jotego/jtcps/doc/measurements/dma/pcb.jpg

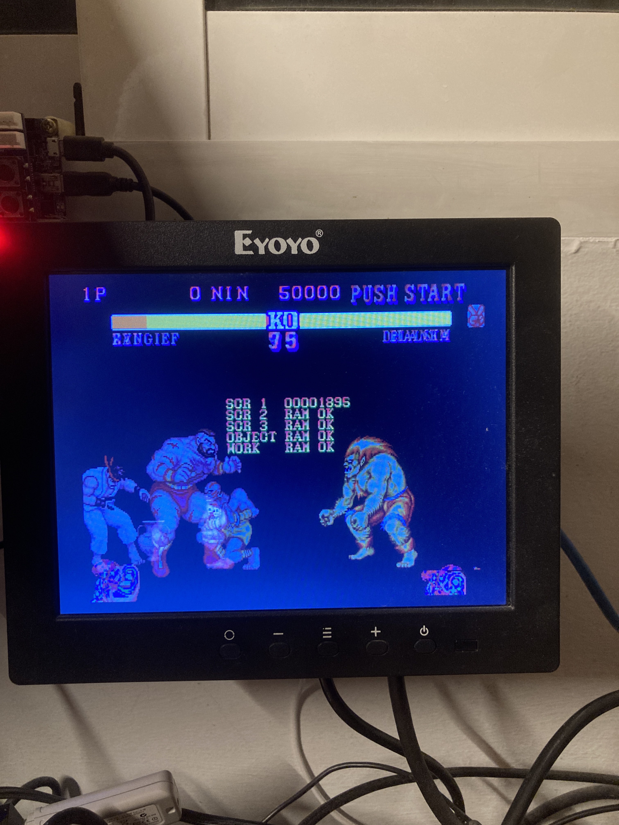
doc/measurements/dma/pcb.jpg
