jotego/jtcps/cores/cps15/ver/game/dino/1.png

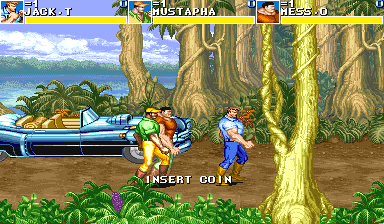
cores/cps15/ver/game/dino/1.png
