jotego/jtcps/cores/cps1/ver/game/sf2/5.png

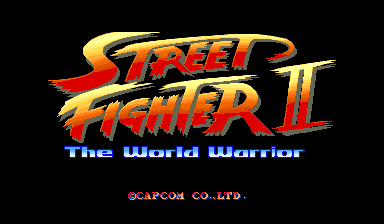
cores/cps1/ver/game/sf2/5.png
