jotego/jtcps/cores/cps1/ver/gfx/0000.png

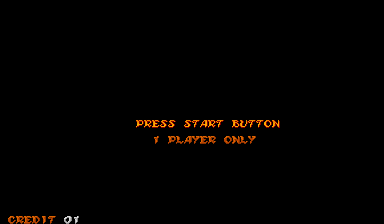
cores/cps1/ver/gfx/0000.png
