jotego/jtcps/cores/cps1/ver/gfx/0001.png

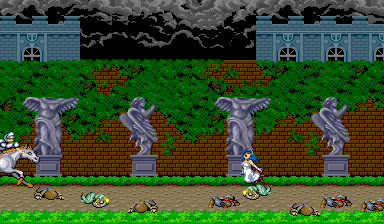
cores/cps1/ver/gfx/0001.png
