jotego/jtcps/doc/cps1-sound/fm_response.png

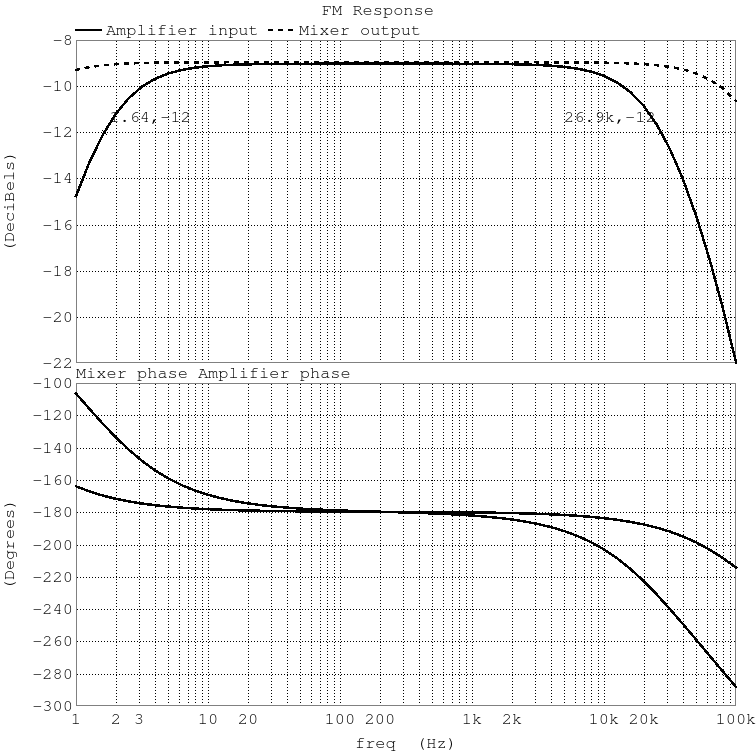
doc/cps1-sound/fm_response.png
