jotego/jtcps/doc/cps1-sound/pcm_response.png

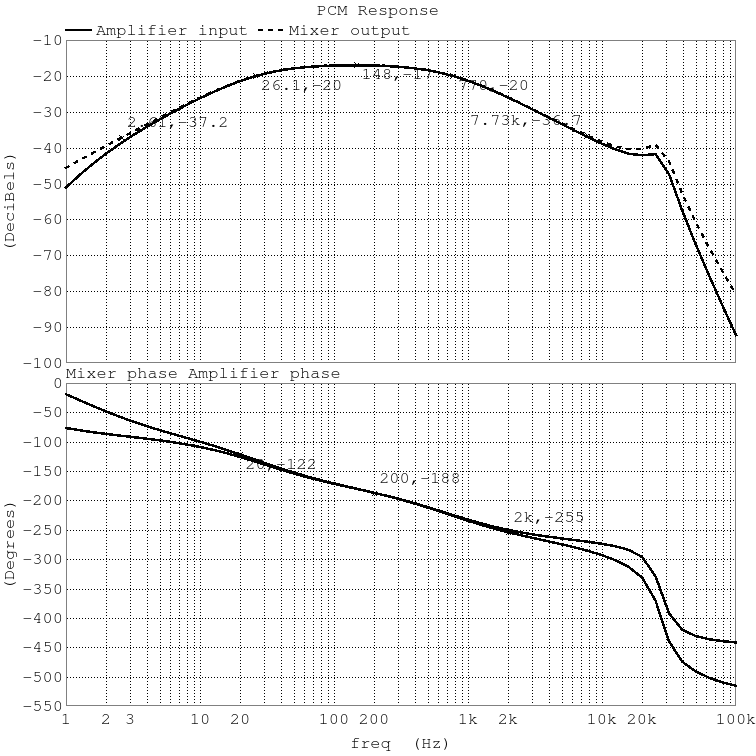
doc/cps1-sound/pcm_response.png
