jotego/jtcps/doc/cps1-sound/fm_step.png

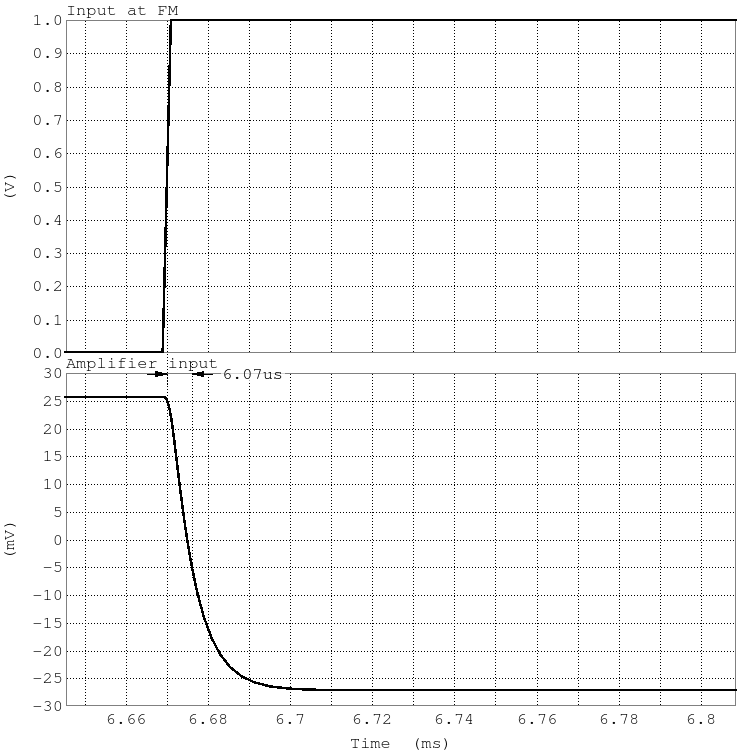
doc/cps1-sound/fm_step.png
