jotego/jtcps/doc/cps1-sound/pcm_step.png

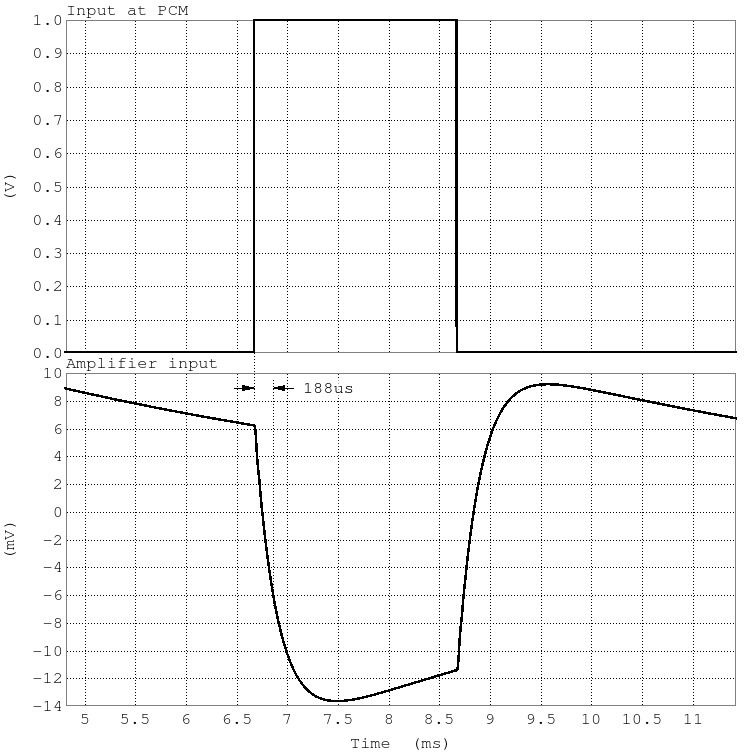
doc/cps1-sound/pcm_step.png
