jotego/jtcps/doc/measurements/DS1Z_QuickPrint2.png

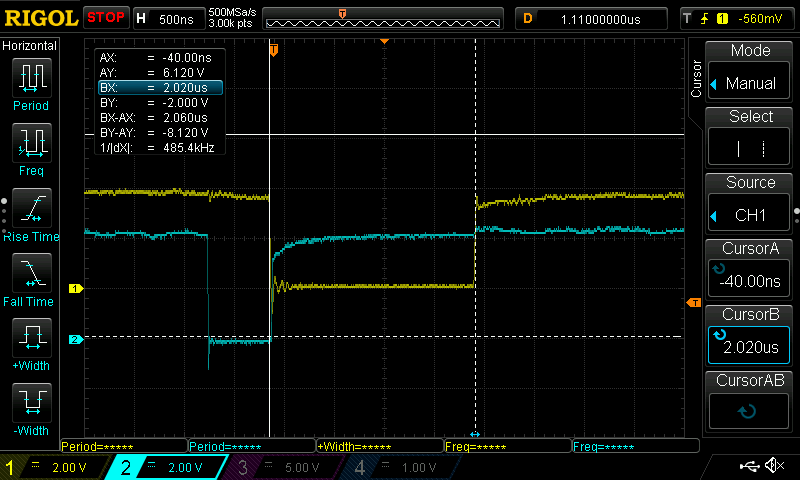
doc/measurements/DS1Z_QuickPrint2.png
