jotego/jtcps/doc/measurements/DS1Z_QuickPrint3.png

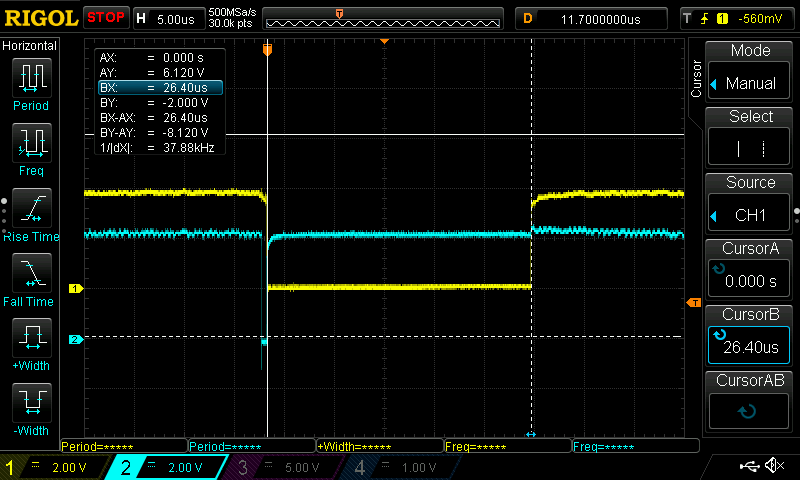
doc/measurements/DS1Z_QuickPrint3.png
