jotego/jtcps/doc/measurements/DS1Z_QuickPrint4.png

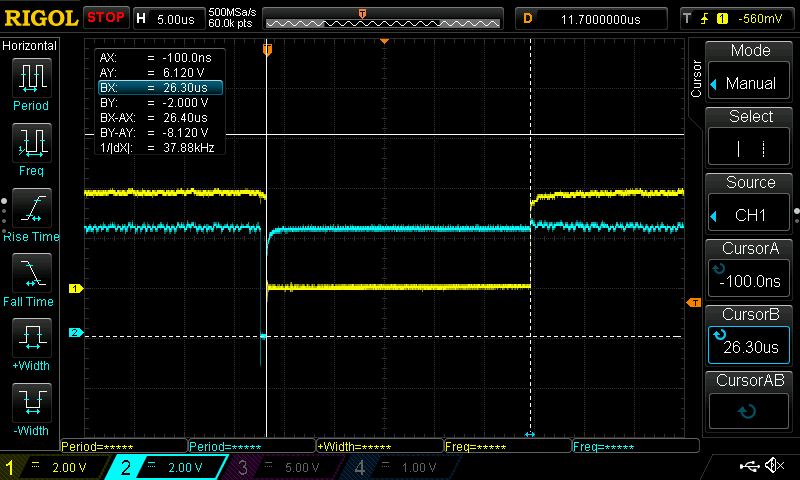
doc/measurements/DS1Z_QuickPrint4.png
