jotego/jtcps/doc/measurements/DS1Z_QuickPrint7.png

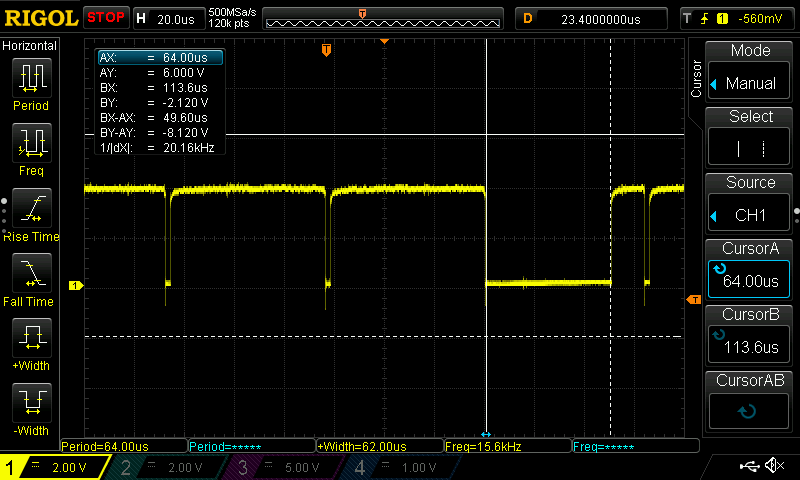
doc/measurements/DS1Z_QuickPrint7.png
