jotego/jtcps/doc/measurements/DS1Z_QuickPrint8.png

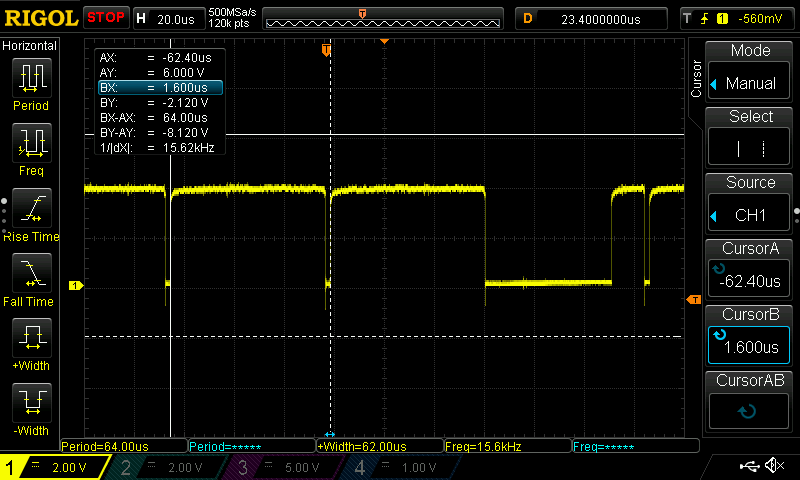
doc/measurements/DS1Z_QuickPrint8.png
