jotego/jtcps/doc/measurements/DS1Z_QuickPrint10.png

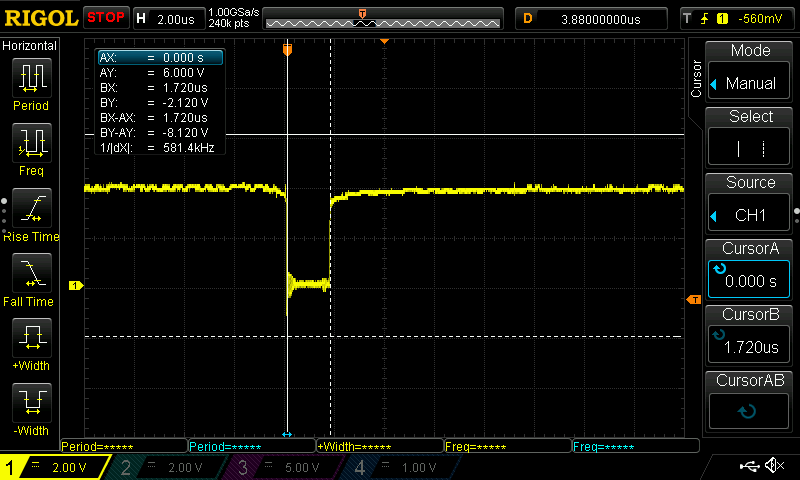
doc/measurements/DS1Z_QuickPrint10.png
