jotego/jtcps/doc/measurements/DS1Z_QuickPrint11.png

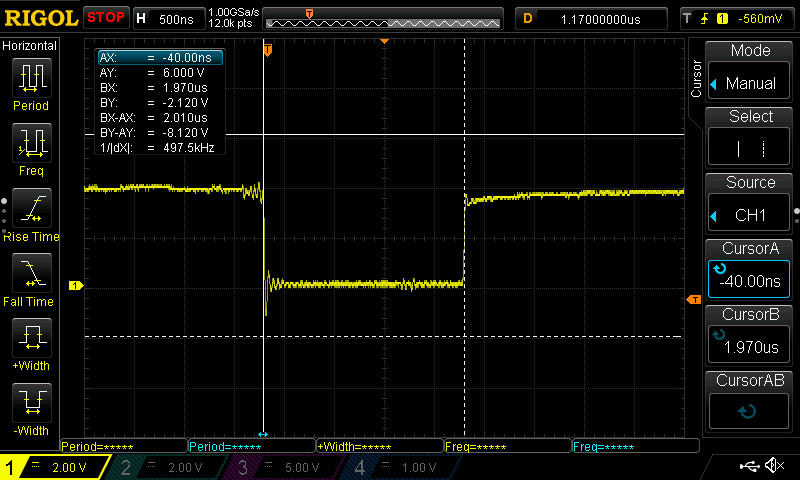
doc/measurements/DS1Z_QuickPrint11.png
