jotego/jtcps/doc/measurements/DS1Z_QuickPrint13.png

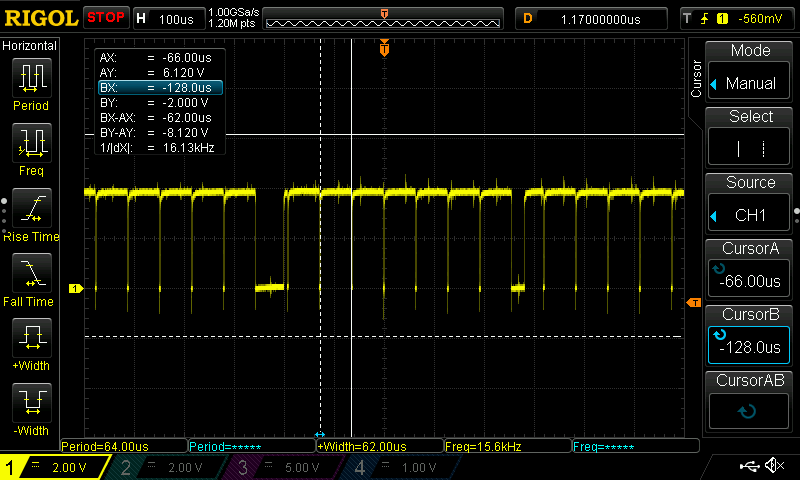
doc/measurements/DS1Z_QuickPrint13.png
