jotego/jtcps/doc/measurements/DS1Z_QuickPrint14.png

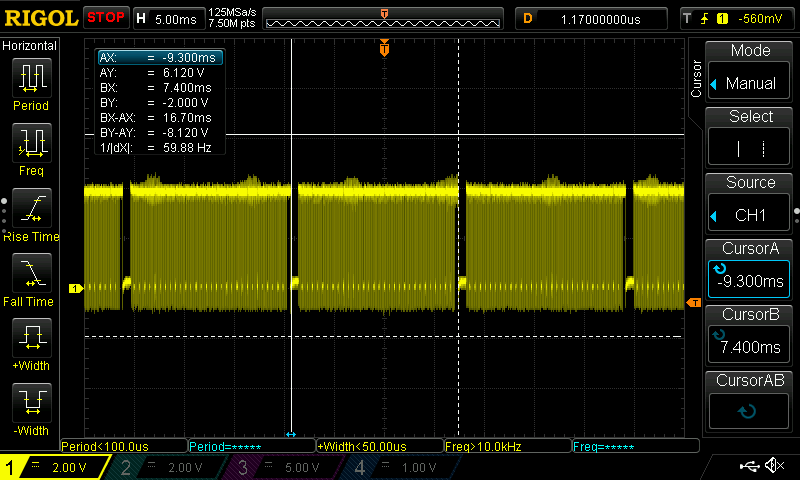
doc/measurements/DS1Z_QuickPrint14.png
