jotego/jtcps/doc/measurements/DS1Z_QuickPrint15.png

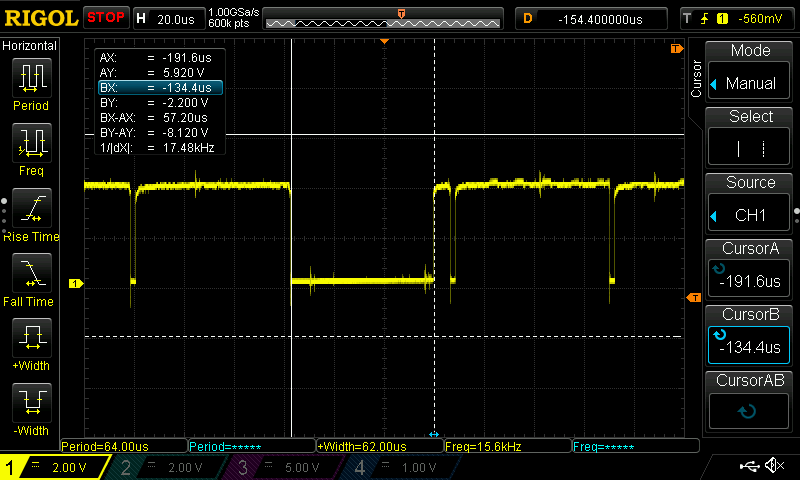
doc/measurements/DS1Z_QuickPrint15.png
