jotego/jtcps/doc/measurements/DS1Z_QuickPrint17.png

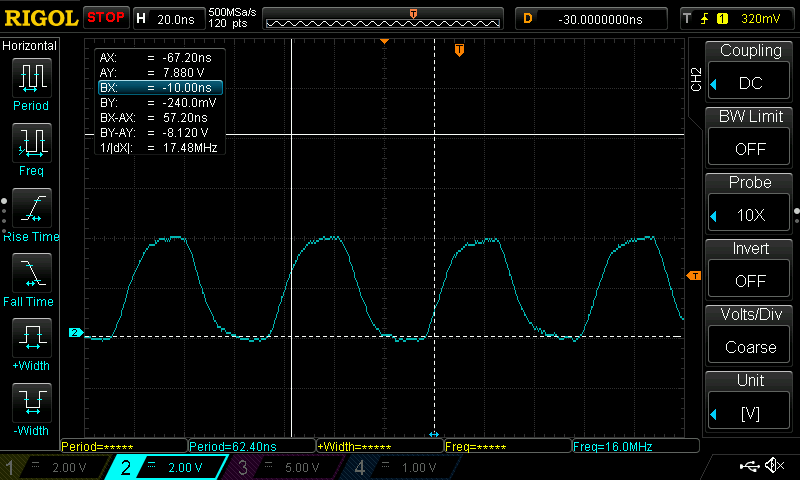
doc/measurements/DS1Z_QuickPrint17.png
