jotego/jtcps/doc/measurements/dma/20210130_182909-screen.png

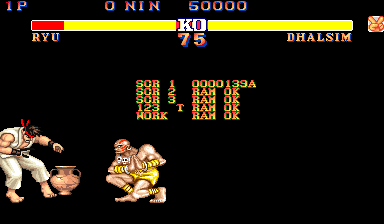
doc/measurements/dma/20210130_182909-screen.png
