jotego/jtcps/doc/measurements/dma/20210130_182920-screen.png

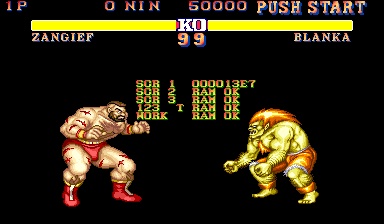
doc/measurements/dma/20210130_182920-screen.png
