jotego/jtcps/doc/measurements/dma/20210130_182930-screen.png

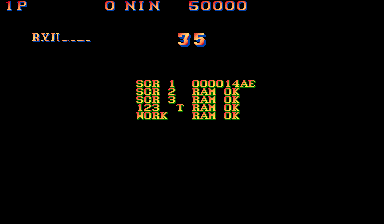
doc/measurements/dma/20210130_182930-screen.png
