jotego/jtcps/cores/cps3/memories.kicad_sch

## KiCad design cores/cps3/memories.kicad_sch (2022-10-21)

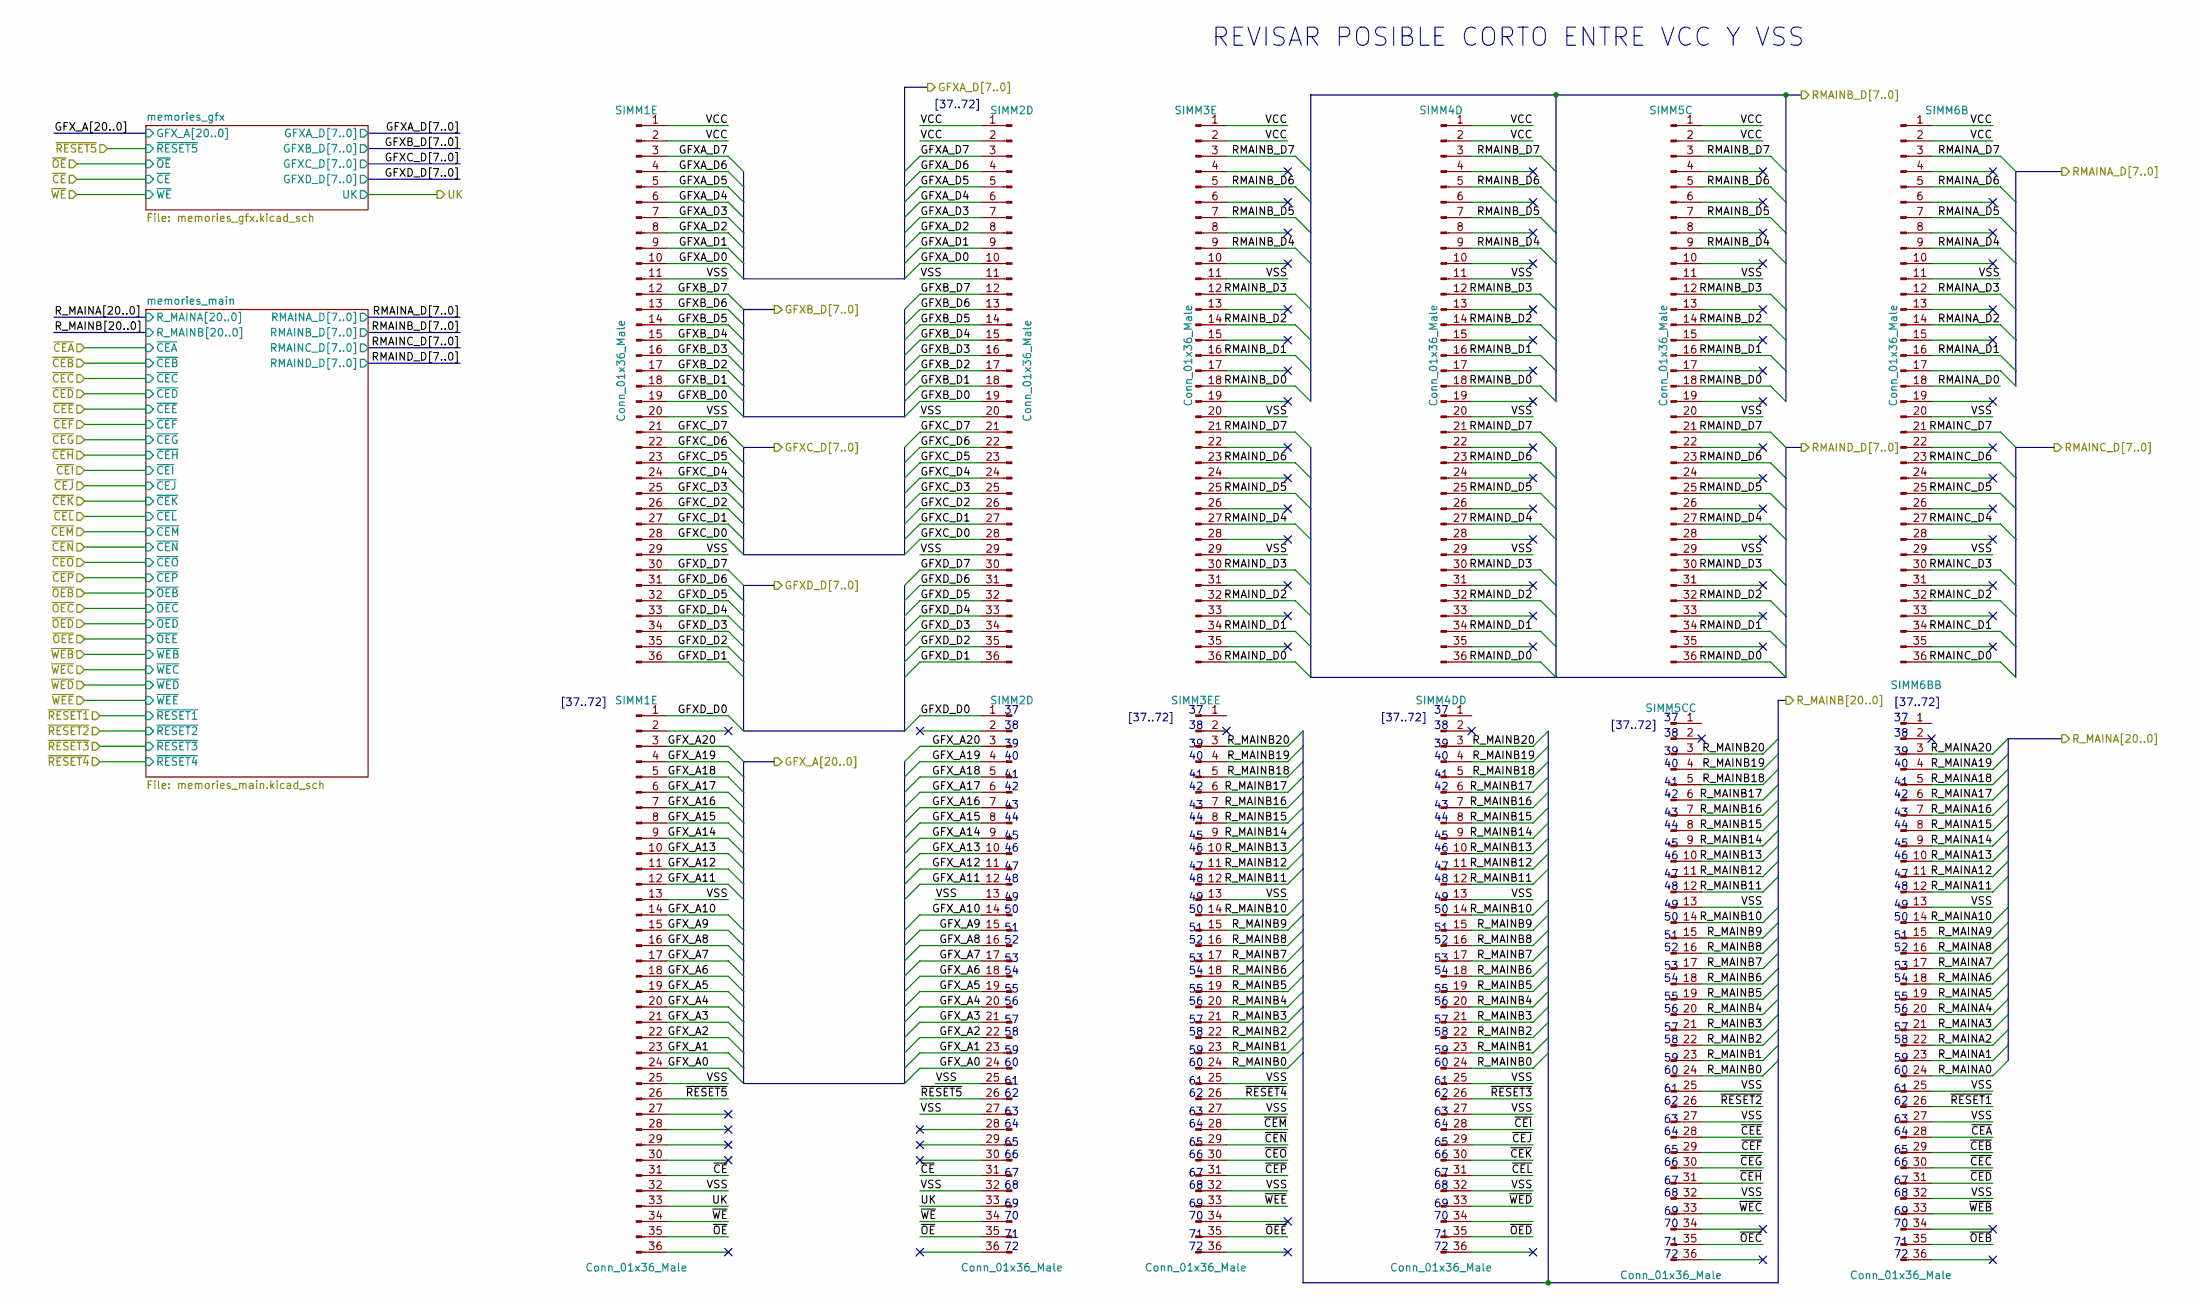
[picture p86: schematic memories.kicad_sch]

Parts:
SIMM1E, SIMM2D, SIMM3E, SIMM3EE, SIMM4D, SIMM4DD, SIMM5C, SIMM5CC, SIMM6B, SIMM6BB: Conn_01x36_Male

Connections:
GFXA_D0: SIMM1E.10, SIMM2D.10
GFXA_D1: SIMM1E.9, SIMM2D.9
GFXA_D2: SIMM1E.8, SIMM2D.8
GFXA_D3: SIMM1E.7, SIMM2D.7
GFXA_D4: SIMM1E.6, SIMM2D.6
GFXA_D5: SIMM1E.5, SIMM2D.5
GFXA_D6: SIMM1E.4, SIMM2D.4
GFXA_D7: SIMM1E.3, SIMM2D.3
GFXB_D0: SIMM1E.19, SIMM2D.19
GFXB_D1: SIMM1E.18, SIMM2D.18
GFXB_D2: SIMM1E.17, SIMM2D.17
GFXB_D3: SIMM1E.16, SIMM2D.16
GFXB_D4: SIMM1E.15, SIMM2D.15
GFXB_D5: SIMM1E.14, SIMM2D.14
GFXB_D6: SIMM1E.13, SIMM2D.13
GFXB_D7: SIMM1E.12, SIMM2D.12
GFXC_D0: SIMM1E.28, SIMM2D.28
GFXC_D1: SIMM1E.27, SIMM2D.27
GFXC_D2: SIMM1E.26, SIMM2D.26
GFXC_D3: SIMM1E.25, SIMM2D.25
GFXC_D4: SIMM1E.24, SIMM2D.24
GFXC_D5: SIMM1E.23, SIMM2D.23
GFXC_D6: SIMM1E.22, SIMM2D.22
GFXC_D7: SIMM1E.21, SIMM2D.21
GFXD_D0: SIMM1E.1, SIMM2D.1
GFXD_D1: SIMM1E.36, SIMM2D.36
GFXD_D2: SIMM1E.35, SIMM2D.35
GFXD_D3: SIMM1E.34, SIMM2D.34
GFXD_D4: SIMM1E.33, SIMM2D.33
GFXD_D5: SIMM1E.32, SIMM2D.32
GFXD_D6: SIMM1E.31, SIMM2D.31
GFXD_D7: SIMM1E.30, SIMM2D.30
GFX_A0: SIMM1E.24, SIMM2D.24
GFX_A1: SIMM1E.23, SIMM2D.23
GFX_A2: SIMM1E.22, SIMM2D.22
GFX_A3: SIMM1E.21, SIMM2D.21
GFX_A4: SIMM1E.20, SIMM2D.20
GFX_A5: SIMM1E.19, SIMM2D.19
GFX_A6: SIMM1E.18, SIMM2D.18
GFX_A7: SIMM1E.17, SIMM2D.17
GFX_A8: SIMM1E.16, SIMM2D.16
GFX_A9: SIMM1E.15, SIMM2D.15
GFX_A10: SIMM1E.14, SIMM2D.14
GFX_A11: SIMM1E.12, SIMM2D.12
GFX_A12: SIMM1E.11, SIMM2D.11
GFX_A13: SIMM1E.10, SIMM2D.10
GFX_A14: SIMM1E.9, SIMM2D.9
GFX_A15: SIMM1E.8, SIMM2D.8
GFX_A16: SIMM1E.7, SIMM2D.7
GFX_A17: SIMM1E.6, SIMM2D.6
GFX_A18: SIMM1E.5, SIMM2D.5
GFX_A19: SIMM1E.4, SIMM2D.4
GFX_A20: SIMM1E.3, SIMM2D.3
RMAINA_D0: SIMM6B.18
RMAINA_D1: SIMM6B.16
RMAINA_D2: SIMM6B.14
RMAINA_D3: SIMM6B.12
RMAINA_D4: SIMM6B.9
RMAINA_D5: SIMM6B.7
RMAINA_D6: SIMM6B.5
RMAINA_D7: SIMM6B.3
RMAINB_D0: SIMM3E.18, SIMM4D.18, SIMM5C.18
RMAINB_D1: SIMM3E.16, SIMM4D.16, SIMM5C.16
RMAINB_D2: SIMM3E.14, SIMM4D.14, SIMM5C.14
RMAINB_D3: SIMM3E.12, SIMM4D.12, SIMM5C.12
RMAINB_D4: SIMM3E.9, SIMM4D.9, SIMM5C.9
RMAINB_D5: SIMM3E.7, SIMM4D.7, SIMM5C.7
RMAINB_D6: SIMM3E.5, SIMM4D.5, SIMM5C.5
RMAINB_D7: SIMM3E.3, SIMM4D.3, SIMM5C.3
RMAINC_D0: SIMM6B.36
RMAINC_D1: SIMM6B.34
RMAINC_D2: SIMM6B.32
RMAINC_D3: SIMM6B.30
RMAINC_D4: SIMM6B.27
RMAINC_D5: SIMM6B.25
RMAINC_D6: SIMM6B.23
RMAINC_D7: SIMM6B.21
RMAIND_D0: SIMM3E.36, SIMM4D.36, SIMM5C.36
RMAIND_D1: SIMM3E.34, SIMM4D.34, SIMM5C.34
RMAIND_D2: SIMM3E.32, SIMM4D.32, SIMM5C.32
RMAIND_D3: SIMM3E.30, SIMM4D.30, SIMM5C.30
RMAIND_D4: SIMM3E.27, SIMM4D.27, SIMM5C.27
RMAIND_D5: SIMM3E.25, SIMM4D.25, SIMM5C.25
RMAIND_D6: SIMM3E.23, SIMM4D.23, SIMM5C.23
RMAIND_D7: SIMM3E.21, SIMM4D.21, SIMM5C.21
R_MAINA0: SIMM6BB.24
R_MAINA1: SIMM6BB.23
R_MAINA2: SIMM6BB.22
R_MAINA3: SIMM6BB.21
R_MAINA4: SIMM6BB.20
R_MAINA5: SIMM6BB.19
R_MAINA6: SIMM6BB.18
R_MAINA7: SIMM6BB.17
R_MAINA8: SIMM6BB.16
R_MAINA9: SIMM6BB.15
R_MAINA10: SIMM6BB.14
R_MAINA11: SIMM6BB.12
R_MAINA12: SIMM6BB.11
R_MAINA13: SIMM6BB.10
R_MAINA14: SIMM6BB.9
R_MAINA15: SIMM6BB.8
R_MAINA16: SIMM6BB.7
R_MAINA17: SIMM6BB.6
R_MAINA18: SIMM6BB.5
R_MAINA19: SIMM6BB.4
R_MAINA20: SIMM6BB.3
R_MAINB0: SIMM3EE.24, SIMM4DD.24, SIMM5CC.24
R_MAINB1: SIMM3EE.23, SIMM4DD.23, SIMM5CC.23
R_MAINB2: SIMM3EE.22, SIMM4DD.22, SIMM5CC.22
R_MAINB3: SIMM3EE.21, SIMM4DD.21, SIMM5CC.21
R_MAINB4: SIMM3EE.20, SIMM4DD.20, SIMM5CC.20
R_MAINB5: SIMM3EE.19, SIMM4DD.19, SIMM5CC.19
R_MAINB6: SIMM3EE.18, SIMM4DD.18, SIMM5CC.18
R_MAINB7: SIMM3EE.17, SIMM4DD.17, SIMM5CC.17
R_MAINB8: SIMM3EE.16, SIMM4DD.16, SIMM5CC.16
R_MAINB9: SIMM3EE.15, SIMM4DD.15, SIMM5CC.15
R_MAINB10: SIMM3EE.14, SIMM4DD.14, SIMM5CC.14
R_MAINB11: SIMM3EE.12, SIMM4DD.12, SIMM5CC.12
R_MAINB12: SIMM3EE.11, SIMM4DD.11, SIMM5CC.11
R_MAINB13: SIMM3EE.10, SIMM4DD.10, SIMM5CC.10
R_MAINB14: SIMM3EE.9, SIMM4DD.9, SIMM5CC.9
R_MAINB15: SIMM3EE.8, SIMM4DD.8, SIMM5CC.8
R_MAINB16: SIMM3EE.7, SIMM4DD.7, SIMM5CC.7
R_MAINB17: SIMM3EE.6, SIMM4DD.6, SIMM5CC.6
R_MAINB18: SIMM3EE.5, SIMM4DD.5, SIMM5CC.5
R_MAINB19: SIMM3EE.4, SIMM4DD.4, SIMM5CC.4
R_MAINB20: SIMM3EE.3, SIMM4DD.3, SIMM5CC.3
UK: SIMM1E.33, SIMM2D.33
VCC: SIMM1E.1, SIMM1E.2, SIMM2D.1, SIMM2D.2, SIMM3E.1, SIMM3E.2, SIMM4D.1, SIMM4D.2, SIMM5C.1, SIMM5C.2, SIMM6B.1, SIMM6B.2
VSS: SIMM1E.11, SIMM1E.13, SIMM1E.20, SIMM1E.25, SIMM1E.29, SIMM1E.32, SIMM2D.11, SIMM2D.13, SIMM2D.20, SIMM2D.25, SIMM2D.27, SIMM2D.29, SIMM2D.32, SIMM3E.11, SIMM3E.20, SIMM3E.29, SIMM3EE.13, SIMM3EE.25, SIMM3EE.27, SIMM3EE.32, SIMM4D.11, SIMM4D.20, SIMM4D.29, SIMM4DD.13, SIMM4DD.25, SIMM4DD.27, SIMM4DD.32, SIMM5C.11, SIMM5C.20, SIMM5C.29, SIMM5CC.13, SIMM5CC.25, SIMM5CC.27, SIMM5CC.32, SIMM6B.11, SIMM6B.20, SIMM6B.29, SIMM6BB.13, SIMM6BB.25, SIMM6BB.27, SIMM6BB.32
~CEA: SIMM6BB.28
~CEB: SIMM6BB.29
~CEC: SIMM6BB.30
~CED: SIMM6BB.31
~CEE: SIMM5CC.28
~CEF: SIMM5CC.29
~CEG: SIMM5CC.30
~CEH: SIMM5CC.31
~CEI: SIMM4DD.28
~CEJ: SIMM4DD.29
~CEK: SIMM4DD.30
~CEL: SIMM4DD.31
~CEM: SIMM3EE.28
~CEN: SIMM3EE.29
~CEO: SIMM3EE.30
~CEP: SIMM3EE.31
~CE: SIMM1E.31, SIMM2D.31
~OEB: SIMM6BB.35
~OEC: SIMM5CC.35
~OED: SIMM4DD.35
~OEE: SIMM3EE.35
~OE: SIMM1E.35, SIMM2D.35
~RESET1: SIMM6BB.26
~RESET2: SIMM5CC.26
~RESET3: SIMM4DD.26
~RESET4: SIMM3EE.26
~RESET5: SIMM1E.26, SIMM2D.26
~WEB: SIMM6BB.33
~WEC: SIMM5CC.33
~WED: SIMM4DD.33
~WEE: SIMM3EE.33
~WE: SIMM1E.34, SIMM2D.34

Notes on the sheet:
59 60
63 64
57 58
39 40
67 68
65 66
55 56
71 72
69 70
61 62
45 46
41 42
53 54
43 44
49 50
47 48
[37..72]
REVISAR POSIBLE CORTO ENTRE VCC Y VSS
51 52
