jotego/jtcps/cores/cps3/memories_gfx.kicad_sch

## KiCad design cores/cps3/memories_gfx.kicad_sch (2022-10-21)

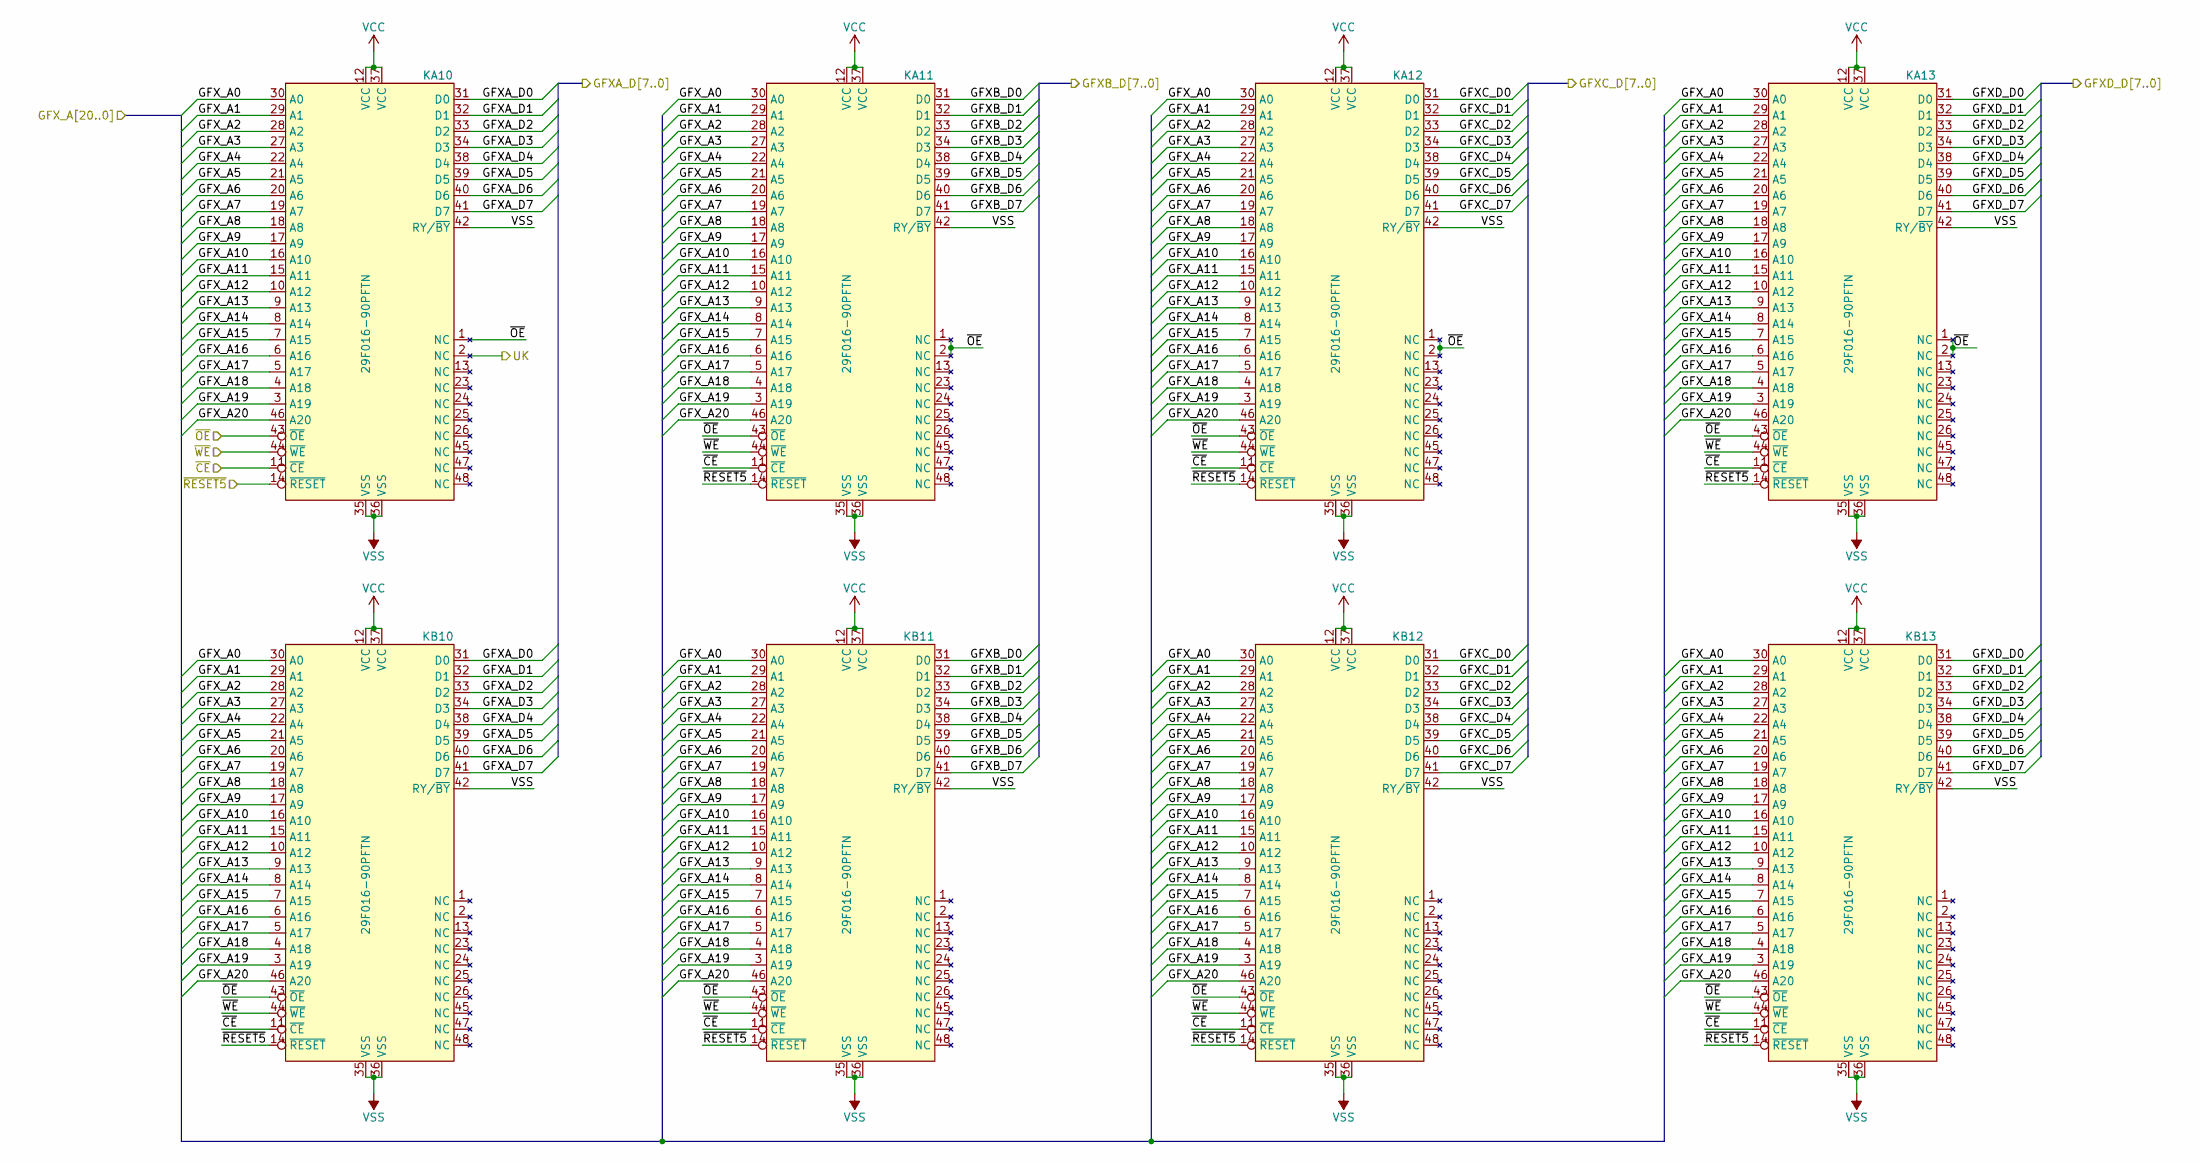
[picture p87: schematic memories_gfx.kicad_sch]

Parts:
KA10, KA11, KA12, KA13: 29F016-90PFTN
KB10, KB11, KB12, KB13: 29F016-90PFTN

Connections:
GFXA_D0: KA10.31 (D0), KB10.31 (D0)
GFXA_D1: KA10.32 (D1), KB10.32 (D1)
GFXA_D2: KA10.33 (D2), KB10.33 (D2)
GFXA_D3: KA10.34 (D3), KB10.34 (D3)
GFXA_D4: KA10.38 (D4), KB10.38 (D4)
GFXA_D5: KA10.39 (D5), KB10.39 (D5)
GFXA_D6: KA10.40 (D6), KB10.40 (D6)
GFXA_D7: KA10.41 (D7), KB10.41 (D7)
GFXB_D0: KA11.31 (D0), KB11.31 (D0)
GFXB_D1: KA11.32 (D1), KB11.32 (D1)
GFXB_D2: KA11.33 (D2), KB11.33 (D2)
GFXB_D3: KA11.34 (D3), KB11.34 (D3)
GFXB_D4: KA11.38 (D4), KB11.38 (D4)
GFXB_D5: KA11.39 (D5), KB11.39 (D5)
GFXB_D6: KA11.40 (D6), KB11.40 (D6)
GFXB_D7: KA11.41 (D7), KB11.41 (D7)
GFXC_D0: KA12.31 (D0), KB12.31 (D0)
GFXC_D1: KA12.32 (D1), KB12.32 (D1)
GFXC_D2: KA12.33 (D2), KB12.33 (D2)
GFXC_D3: KA12.34 (D3), KB12.34 (D3)
GFXC_D4: KA12.38 (D4), KB12.38 (D4)
GFXC_D5: KA12.39 (D5), KB12.39 (D5)
GFXC_D6: KA12.40 (D6), KB12.40 (D6)
GFXC_D7: KA12.41 (D7), KB12.41 (D7)
GFXD_D0: KA13.31 (D0), KB13.31 (D0)
GFXD_D1: KA13.32 (D1), KB13.32 (D1)
GFXD_D2: KA13.33 (D2), KB13.33 (D2)
GFXD_D3: KA13.34 (D3), KB13.34 (D3)
GFXD_D4: KA13.38 (D4), KB13.38 (D4)
GFXD_D5: KA13.39 (D5), KB13.39 (D5)
GFXD_D6: KA13.40 (D6), KB13.40 (D6)
GFXD_D7: KA13.41 (D7), KB13.41 (D7)
GFX_A0: KA10.30 (A0), KA11.30 (A0), KA12.30 (A0), KA13.30 (A0), KB10.30 (A0), KB11.30 (A0), KB12.30 (A0), KB13.30 (A0)
GFX_A1: KA10.29 (A1), KA11.29 (A1), KA12.29 (A1), KA13.29 (A1), KB10.29 (A1), KB11.29 (A1), KB12.29 (A1), KB13.29 (A1)
GFX_A2: KA10.28 (A2), KA11.28 (A2), KA12.28 (A2), KA13.28 (A2), KB10.28 (A2), KB11.28 (A2), KB12.28 (A2), KB13.28 (A2)
GFX_A3: KA10.27 (A3), KA11.27 (A3), KA12.27 (A3), KA13.27 (A3), KB10.27 (A3), KB11.27 (A3), KB12.27 (A3), KB13.27 (A3)
GFX_A4: KA10.22 (A4), KA11.22 (A4), KA12.22 (A4), KA13.22 (A4), KB10.22 (A4), KB11.22 (A4), KB12.22 (A4), KB13.22 (A4)
GFX_A5: KA10.21 (A5), KA11.21 (A5), KA12.21 (A5), KA13.21 (A5), KB10.21 (A5), KB11.21 (A5), KB12.21 (A5), KB13.21 (A5)
GFX_A6: KA10.20 (A6), KA11.20 (A6), KA12.20 (A6), KA13.20 (A6), KB10.20 (A6), KB11.20 (A6), KB12.20 (A6), KB13.20 (A6)
GFX_A7: KA10.19 (A7), KA11.19 (A7), KA12.19 (A7), KA13.19 (A7), KB10.19 (A7), KB11.19 (A7), KB12.19 (A7), KB13.19 (A7)
GFX_A8: KA10.18 (A8), KA11.18 (A8), KA12.18 (A8), KA13.18 (A8), KB10.18 (A8), KB11.18 (A8), KB12.18 (A8), KB13.18 (A8)
GFX_A9: KA10.17 (A9), KA11.17 (A9), KA12.17 (A9), KA13.17 (A9), KB10.17 (A9), KB11.17 (A9), KB12.17 (A9), KB13.17 (A9)
GFX_A10: KA10.16 (A10), KA11.16 (A10), KA12.16 (A10), KA13.16 (A10), KB10.16 (A10), KB11.16 (A10), KB12.16 (A10), KB13.16 (A10)
GFX_A11: KA10.15 (A11), KA11.15 (A11), KA12.15 (A11), KA13.15 (A11), KB10.15 (A11), KB11.15 (A11), KB12.15 (A11), KB13.15 (A11)
GFX_A12: KA10.10 (A12), KA11.10 (A12), KA12.10 (A12), KA13.10 (A12), KB10.10 (A12), KB11.10 (A12), KB12.10 (A12), KB13.10 (A12)
GFX_A13: KA10.9 (A13), KA11.9 (A13), KA12.9 (A13), KA13.9 (A13), KB10.9 (A13), KB11.9 (A13), KB12.9 (A13), KB13.9 (A13)
GFX_A14: KA10.8 (A14), KA11.8 (A14), KA12.8 (A14), KA13.8 (A14), KB10.8 (A14), KB11.8 (A14), KB12.8 (A14), KB13.8 (A14)
GFX_A15: KA10.7 (A15), KA11.7 (A15), KA12.7 (A15), KA13.7 (A15), KB10.7 (A15), KB11.7 (A15), KB12.7 (A15), KB13.7 (A15)
GFX_A16: KA10.6 (A16), KA11.6 (A16), KA12.6 (A16), KA13.6 (A16), KB10.6 (A16), KB11.6 (A16), KB12.6 (A16), KB13.6 (A16)
GFX_A17: KA10.5 (A17), KA11.5 (A17), KA12.5 (A17), KA13.5 (A17), KB10.5 (A17), KB11.5 (A17), KB12.5 (A17), KB13.5 (A17)
GFX_A18: KA10.4 (A18), KA11.4 (A18), KA12.4 (A18), KA13.4 (A18), KB10.4 (A18), KB11.4 (A18), KB12.4 (A18), KB13.4 (A18)
GFX_A19: KA10.3 (A19), KA11.3 (A19), KA12.3 (A19), KA13.3 (A19), KB10.3 (A19), KB11.3 (A19), KB12.3 (A19), KB13.3 (A19)
GFX_A20: KA10.46 (A20), KA11.46 (A20), KA12.46 (A20), KA13.46 (A20), KB10.46 (A20), KB11.46 (A20), KB12.46 (A20), KB13.46 (A20)
unnamed: KA10.12 (VCC), KA10.37 (VCC)
unnamed: KA10.35 (VSS), KA10.36 (VSS)
unnamed: KA10., KA10.23 (NC)
unnamed: KA11.12 (VCC), KA11.37 (VCC)
unnamed: KA11.35 (VSS), KA11.36 (VSS)
unnamed: KA11., KA11.23 (NC)
unnamed: KA12.12 (VCC), KA12.37 (VCC)
unnamed: KA12.35 (VSS), KA12.36 (VSS)
unnamed: KA12., KA12.23 (NC)
unnamed: KA13.12 (VCC), KA13.37 (VCC)
unnamed: KA13.35 (VSS), KA13.36 (VSS)
unnamed: KA13., KA13.23 (NC)
unnamed: KB10.12 (VCC), KB10.37 (VCC)
unnamed: KB10.35 (VSS), KB10.36 (VSS)
unnamed: KB10., KB10.23 (NC)
unnamed: KB11.12 (VCC), KB11.37 (VCC)
unnamed: KB11.35 (VSS), KB11.36 (VSS)
unnamed: KB11., KB11.23 (NC)
unnamed: KB12.12 (VCC), KB12.37 (VCC)
unnamed: KB12.35 (VSS), KB12.36 (VSS)
unnamed: KB12., KB12.23 (NC)
unnamed: KB13.12 (VCC), KB13.37 (VCC)
unnamed: KB13.35 (VSS), KB13.36 (VSS)
unnamed: KB13., KB13.23 (NC)
UK: KA10.2 (NC)
VSS: KA10.42 (RY/~BY), KA11.42 (RY/~BY), KA12.42 (RY/~BY), KA13.42 (RY/~BY), KB10.42 (RY/~BY), KB11.42 (RY/~BY), KB12.42 (RY/~BY), KB13.42 (RY/~BY)
~CE: KA10.11 (~CE), KA11.11 (~CE), KA12.11 (~CE), KA13.11 (~CE), KB10.11 (~CE), KB11.11 (~CE), KB12.11 (~CE), KB13.11 (~CE)
~OE: KA10.1 (NC), KA10.43 (~OE), KA11.1 (NC), KA11.2 (NC), KA11.43 (~OE), KA12.1 (NC), KA12.2 (NC), KA12.43 (~OE), KA13.1 (NC), KA13.2 (NC), KA13.43 (~OE), KB10.43 (~OE), KB11.43 (~OE), KB12.43 (~OE), KB13.43 (~OE)
~RESET5: KA10.14 (~RESET), KA11.14 (~RESET), KA12.14 (~RESET), KA13.14 (~RESET), KB10.14 (~RESET), KB11.14 (~RESET), KB12.14 (~RESET), KB13.14 (~RESET)
~WE: KA10.44 (~WE), KA11.44 (~WE), KA12.44 (~WE), KA13.44 (~WE), KB10.44 (~WE), KB11.44 (~WE), KB12.44 (~WE), KB13.44 (~WE)
