jotego/jtcps/cores/cps3/sch/blanking.kicad_sch

## KiCad design cores/cps3/sch/blanking.kicad_sch (2022-12-15)

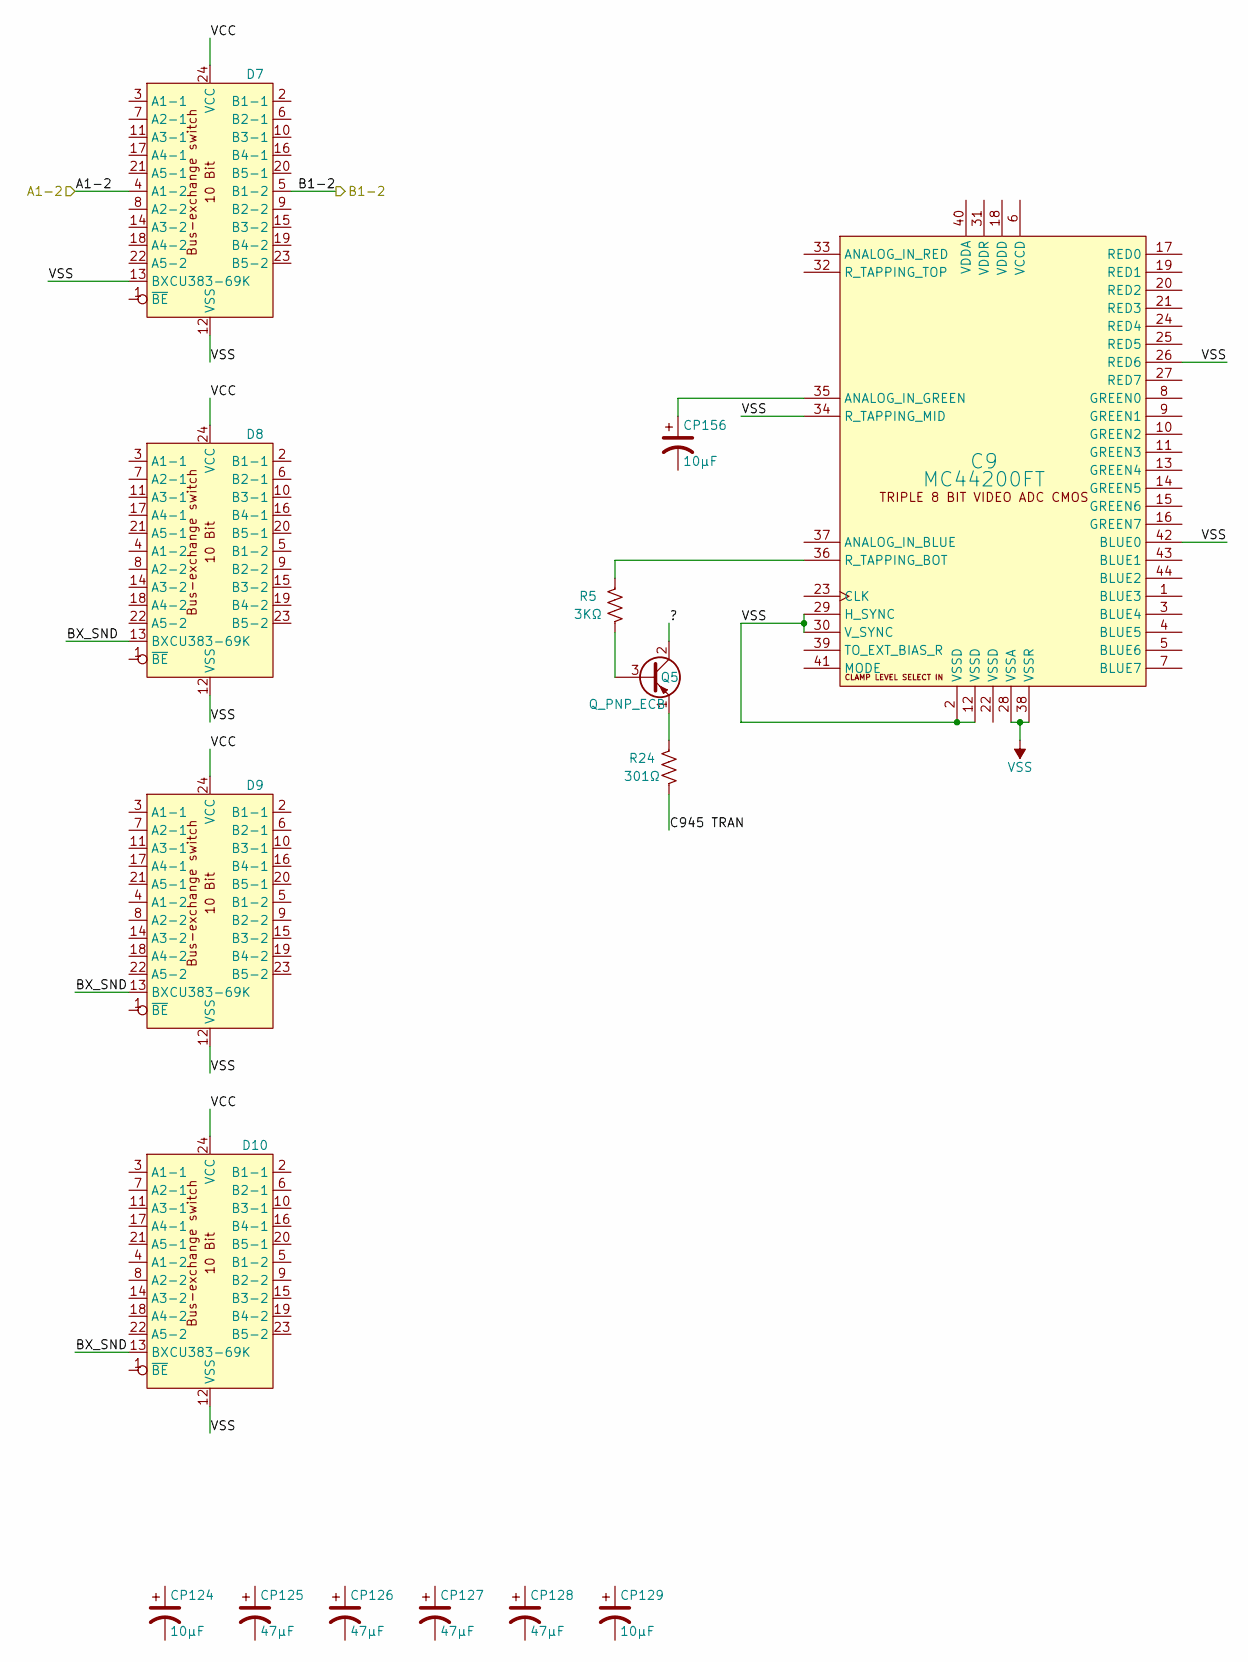
[picture p90: schematic blanking.kicad_sch]

Parts:
C9: MC44200FT
CP124, CP129, CP156: 10μF
CP125, CP126, CP127, CP128: 47μF
D7, D8, D9, D10: CU383-69K
Q5: Q_PNP_ECB
R5: 3KΩ
R24: 301Ω

Connections:
?: Q5.2 (C)
A1-2: D7.4 (A1-2)
B1-2: D7.5 (B1-2)
BX_SND: D8.13 (BX), D9.13 (BX), D10.13 (BX)
C945 TRAN: R24.2
unnamed: C9.28 (VSSA), C9.38 (VSSR)
unnamed: C9.35 (ANALOG_IN_GREEN), CP156.1
unnamed: C9.36 (R_TAPPING_BOT), R5.1
unnamed: Q5.1 (E), R24.1
unnamed: Q5.3 (B), R5.2
VCC: D7.24 (VCC), D8.24 (VCC), D9.24 (VCC), D10.24 (VCC)
VSS: C9.2 (VSSD), C9.12 (VSSD), C9.26 (RED6), C9.29 (H_SYNC), C9.30 (V_SYNC), C9.34 (R_TAPPING_MID), C9.42 (BLUE0), D7.12 (VSS), D7.13 (BX), D8.12 (VSS), D9.12 (VSS), D10.12 (VSS)
