jotego/jtcps/cores/cps3/sch/cps3.kicad_sch

## KiCad design cores/cps3/sch/cps3.kicad_sch (2023-02-07, an earlier design)

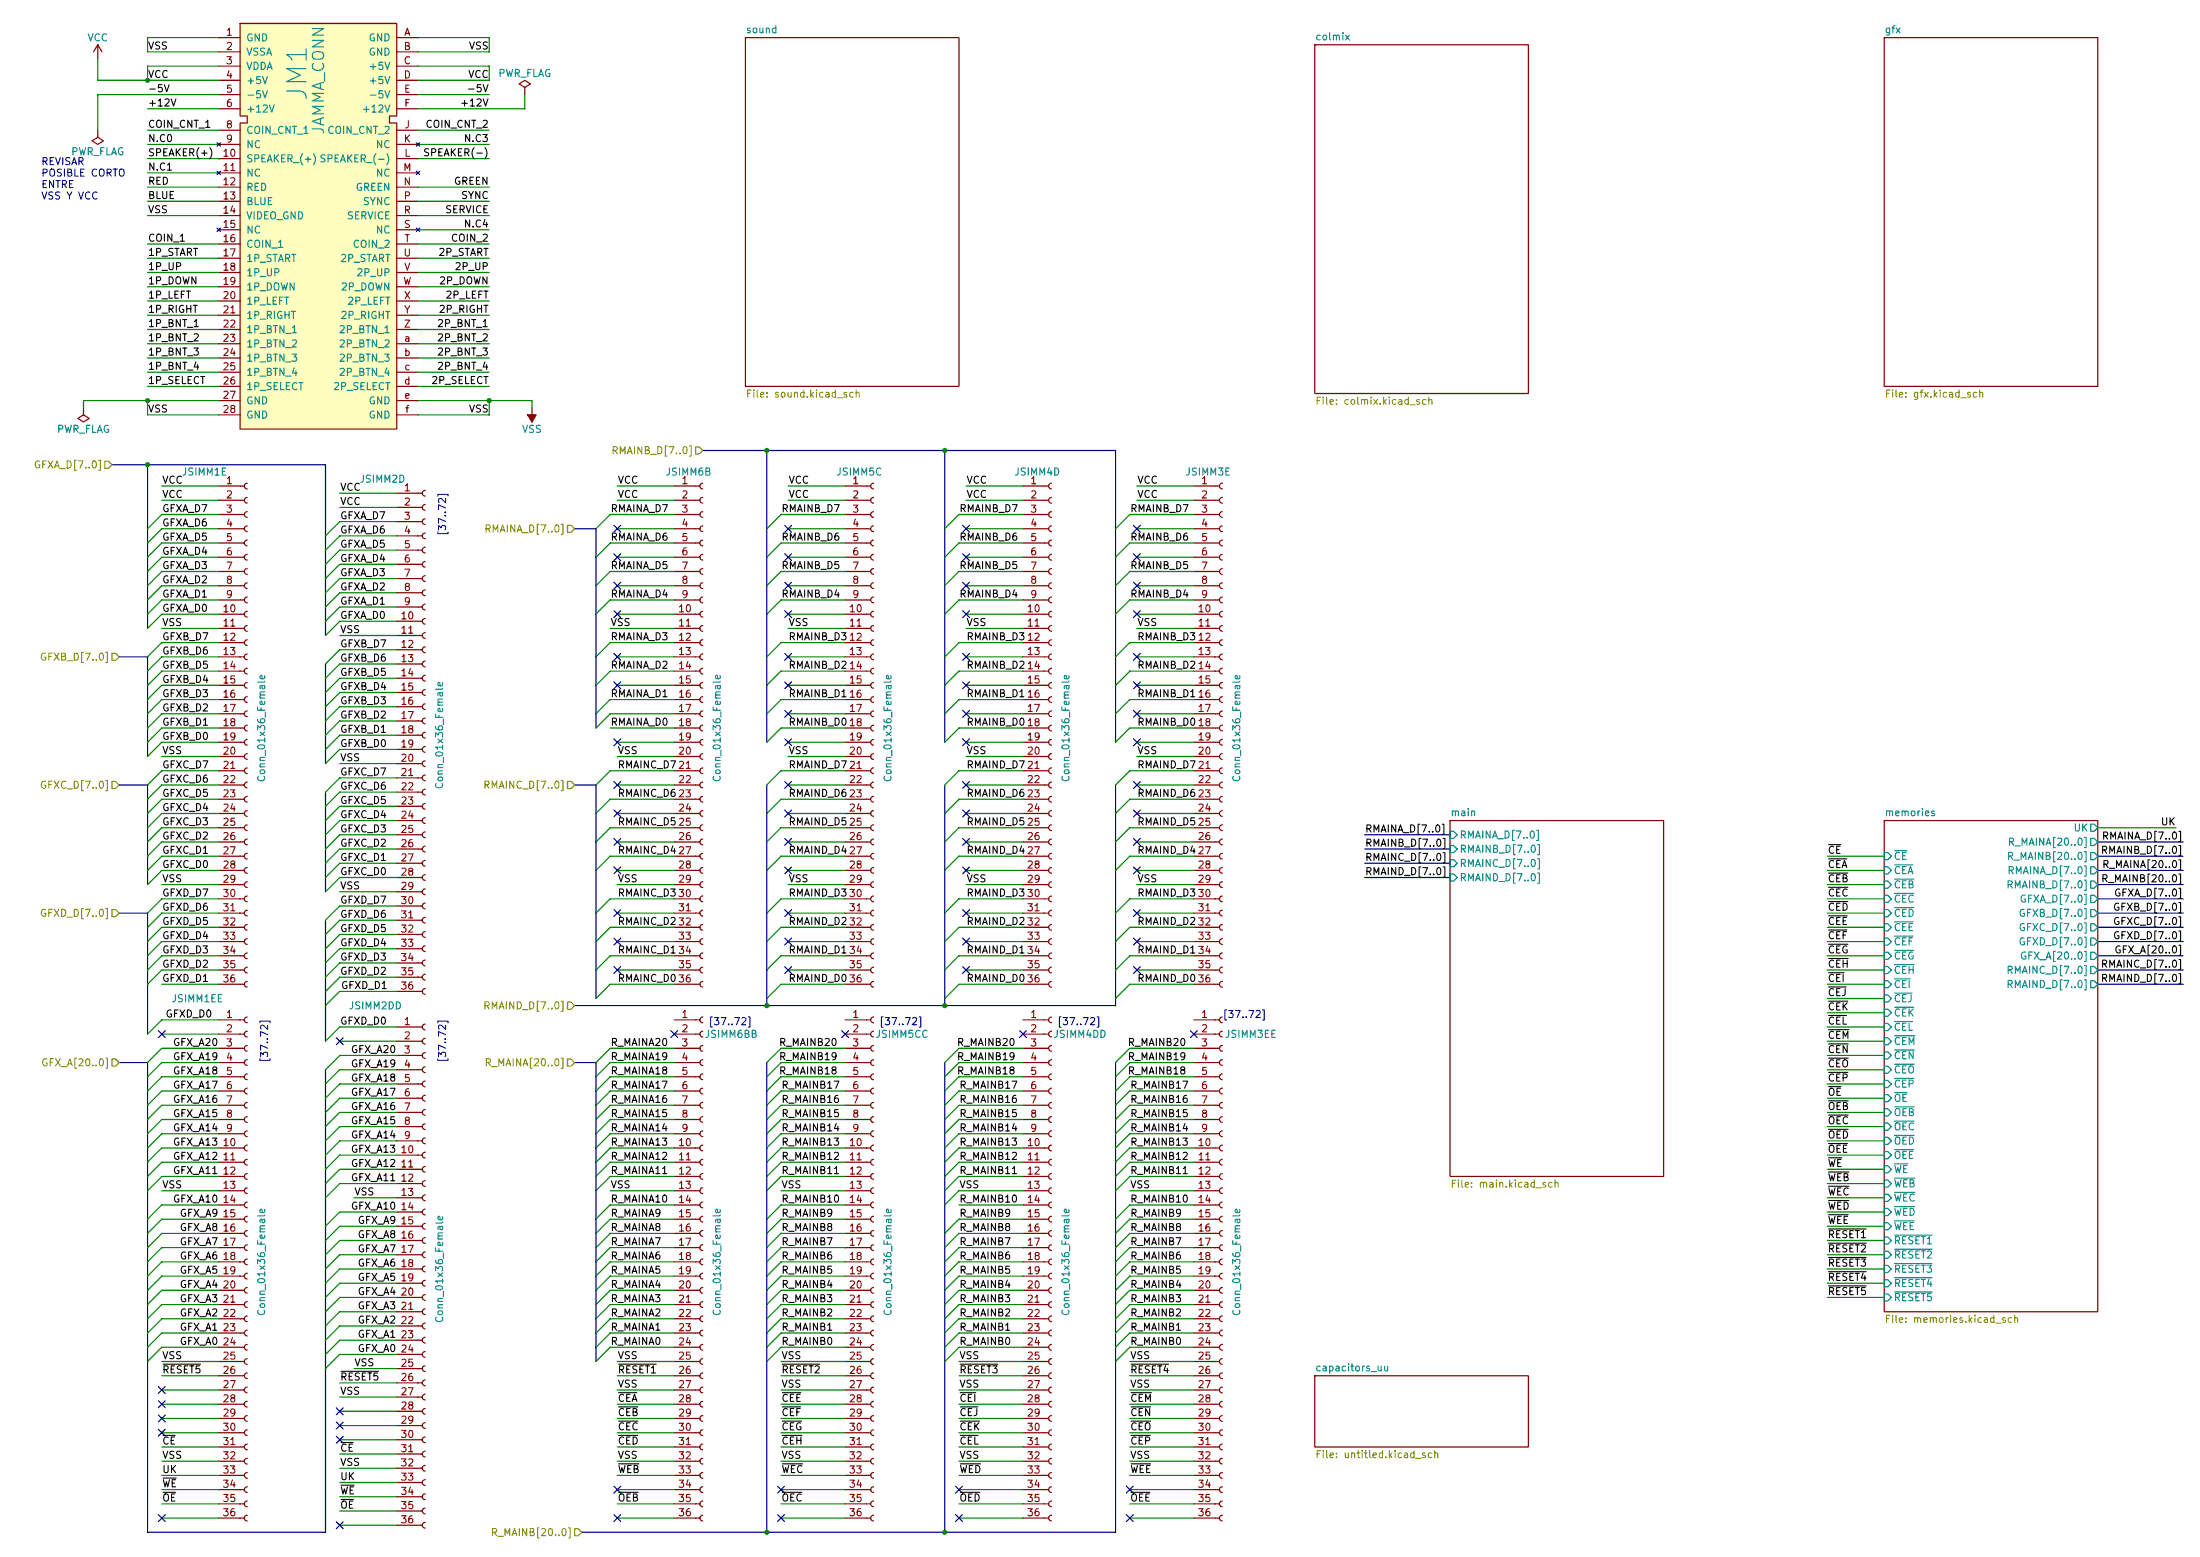
[picture p94: schematic cps3.kicad_sch]

Parts:
JM1: JAMMA_CONN
JSIMM1E, JSIMM1EE, JSIMM2D, JSIMM2DD, JSIMM3E, JSIMM3EE, JSIMM4D, JSIMM4DD, JSIMM5C, JSIMM5CC, JSIMM6B, JSIMM6BB: Conn_01x36_Female

Connections:
1P_BNT_1: JM1.22 (1P_BTN_1)
1P_BNT_2: JM1.23 (1P_BTN_2)
1P_BNT_3: JM1.24 (1P_BTN_3)
1P_BNT_4: JM1.25 (1P_BTN_4)
1P_DOWN: JM1.19 (1P_DOWN)
1P_LEFT: JM1.20 (1P_LEFT)
1P_RIGHT: JM1.21 (1P_RIGHT)
1P_SELECT: JM1.26 (1P_SELECT)
1P_START: JM1.17 (1P_START)
1P_UP: JM1.18 (1P_UP)
2P_BNT_1: JM1.Z (2P_BTN_1)
2P_BNT_2: JM1.a (2P_BTN_2)
2P_BNT_3: JM1.b (2P_BTN_3)
2P_BNT_4: JM1.c (2P_BTN_4)
2P_DOWN: JM1.W (2P_DOWN)
2P_LEFT: JM1.X (2P_LEFT)
2P_RIGHT: JM1.Y (2P_RIGHT)
2P_SELECT: JM1.d (2P_SELECT)
2P_START: JM1.U (2P_START)
2P_UP: JM1.V (2P_UP)
+12V: JM1.6 (+12V), JM1.F (+12V)
-5V: JM1.5 (-5V), JM1.E (-5V)
BLUE: JM1.13 (BLUE)
COIN_1: JM1.16 (COIN_1)
COIN_2: JM1.T (COIN_2)
COIN_CNT_1: JM1.8 (COIN_CNT_1)
COIN_CNT_2: JM1.J (COIN_CNT_2)
GFXA_D0: JSIMM1E.10, JSIMM2D.10
GFXA_D1: JSIMM1E.9, JSIMM2D.9
GFXA_D2: JSIMM1E.8, JSIMM2D.8
GFXA_D3: JSIMM1E.7, JSIMM2D.7
GFXA_D4: JSIMM1E.6, JSIMM2D.6
GFXA_D5: JSIMM1E.5, JSIMM2D.5
GFXA_D6: JSIMM1E.4, JSIMM2D.4
GFXA_D7: JSIMM1E.3, JSIMM2D.3
GFXB_D0: JSIMM1E.19, JSIMM2D.19
GFXB_D1: JSIMM1E.18, JSIMM2D.18
GFXB_D2: JSIMM1E.17, JSIMM2D.17
GFXB_D3: JSIMM1E.16, JSIMM2D.16
GFXB_D4: JSIMM1E.15, JSIMM2D.15
GFXB_D5: JSIMM1E.14, JSIMM2D.14
GFXB_D6: JSIMM1E.13, JSIMM2D.13
GFXB_D7: JSIMM1E.12, JSIMM2D.12
GFXC_D0: JSIMM1E.28, JSIMM2D.28
GFXC_D1: JSIMM1E.27, JSIMM2D.27
GFXC_D2: JSIMM1E.26, JSIMM2D.26
GFXC_D3: JSIMM1E.25, JSIMM2D.25
GFXC_D4: JSIMM1E.24, JSIMM2D.24
GFXC_D5: JSIMM1E.23, JSIMM2D.23
GFXC_D6: JSIMM1E.22, JSIMM2D.22
GFXC_D7: JSIMM1E.21, JSIMM2D.21
GFXD_D0: JSIMM1EE.1, JSIMM2DD.1
GFXD_D1: JSIMM1E.36, JSIMM2D.36
GFXD_D2: JSIMM1E.35, JSIMM2D.35
GFXD_D3: JSIMM1E.34, JSIMM2D.34
GFXD_D4: JSIMM1E.33, JSIMM2D.33
GFXD_D5: JSIMM1E.32, JSIMM2D.32
GFXD_D6: JSIMM1E.31, JSIMM2D.31
GFXD_D7: JSIMM1E.30, JSIMM2D.30
GFX_A0: JSIMM1EE.24, JSIMM2DD.24
GFX_A1: JSIMM1EE.23, JSIMM2DD.23
GFX_A2: JSIMM1EE.22, JSIMM2DD.22
GFX_A3: JSIMM1EE.21, JSIMM2DD.21
GFX_A4: JSIMM1EE.20, JSIMM2DD.20
GFX_A5: JSIMM1EE.19, JSIMM2DD.19
GFX_A6: JSIMM1EE.18, JSIMM2DD.18
GFX_A7: JSIMM1EE.17, JSIMM2DD.17
GFX_A8: JSIMM1EE.16, JSIMM2DD.16
GFX_A9: JSIMM1EE.15, JSIMM2DD.15
GFX_A10: JSIMM1EE.14, JSIMM2DD.14
GFX_A11: JSIMM1EE.12, JSIMM2DD.12
GFX_A12: JSIMM1EE.11, JSIMM2DD.11
GFX_A13: JSIMM1EE.10, JSIMM2DD.10
GFX_A14: JSIMM1EE.9, JSIMM2DD.9
GFX_A15: JSIMM1EE.8, JSIMM2DD.8
GFX_A16: JSIMM1EE.7, JSIMM2DD.7
GFX_A17: JSIMM1EE.6, JSIMM2DD.6
GFX_A18: JSIMM1EE.5, JSIMM2DD.5
GFX_A19: JSIMM1EE.4, JSIMM2DD.4
GFX_A20: JSIMM1EE.3, JSIMM2DD.3
GREEN: JM1.N (GREEN)
N.C0: JM1.9 (NC)
N.C1: JM1.11 (NC)
N.C3: JM1.K (NC)
N.C4: JM1.S (NC)
RED: JM1.12 (RED)
RMAINA_D0: JSIMM6B.18
RMAINA_D1: JSIMM6B.16
RMAINA_D2: JSIMM6B.14
RMAINA_D3: JSIMM6B.12
RMAINA_D4: JSIMM6B.9
RMAINA_D5: JSIMM6B.7
RMAINA_D6: JSIMM6B.5
RMAINA_D7: JSIMM6B.3
RMAINB_D0: JSIMM3E.18, JSIMM4D.18, JSIMM5C.18
RMAINB_D1: JSIMM3E.16, JSIMM4D.16, JSIMM5C.16
RMAINB_D2: JSIMM3E.14, JSIMM4D.14, JSIMM5C.14
RMAINB_D3: JSIMM3E.12, JSIMM4D.12, JSIMM5C.12
RMAINB_D4: JSIMM3E.9, JSIMM4D.9, JSIMM5C.9
RMAINB_D5: JSIMM3E.7, JSIMM4D.7, JSIMM5C.7
RMAINB_D6: JSIMM3E.5, JSIMM4D.5, JSIMM5C.5
RMAINB_D7: JSIMM3E.3, JSIMM4D.3, JSIMM5C.3
RMAINC_D0: JSIMM6B.36
RMAINC_D1: JSIMM6B.34
RMAINC_D2: JSIMM6B.32
RMAINC_D3: JSIMM6B.30
RMAINC_D4: JSIMM6B.27
RMAINC_D5: JSIMM6B.25
RMAINC_D6: JSIMM6B.23
RMAINC_D7: JSIMM6B.21
RMAIND_D0: JSIMM3E.36, JSIMM4D.36, JSIMM5C.36
RMAIND_D1: JSIMM3E.34, JSIMM4D.34, JSIMM5C.34
RMAIND_D2: JSIMM3E.32, JSIMM4D.32, JSIMM5C.32
RMAIND_D3: JSIMM3E.30, JSIMM4D.30, JSIMM5C.30
RMAIND_D4: JSIMM3E.27, JSIMM4D.27, JSIMM5C.27
RMAIND_D5: JSIMM3E.25, JSIMM4D.25, JSIMM5C.25
RMAIND_D6: JSIMM3E.23, JSIMM4D.23, JSIMM5C.23
RMAIND_D7: JSIMM3E.21, JSIMM4D.21, JSIMM5C.21
R_MAINA0: JSIMM6BB.24
R_MAINA1: JSIMM6BB.23
R_MAINA2: JSIMM6BB.22
R_MAINA3: JSIMM6BB.21
R_MAINA4: JSIMM6BB.20
R_MAINA5: JSIMM6BB.19
R_MAINA6: JSIMM6BB.18
R_MAINA7: JSIMM6BB.17
R_MAINA8: JSIMM6BB.16
R_MAINA9: JSIMM6BB.15
R_MAINA10: JSIMM6BB.14
R_MAINA11: JSIMM6BB.12
R_MAINA12: JSIMM6BB.11
R_MAINA13: JSIMM6BB.10
R_MAINA14: JSIMM6BB.9
R_MAINA15: JSIMM6BB.8
R_MAINA16: JSIMM6BB.7
R_MAINA17: JSIMM6BB.6
R_MAINA18: JSIMM6BB.5
R_MAINA19: JSIMM6BB.4
R_MAINA20: JSIMM6BB.3
R_MAINB0: JSIMM3EE.24, JSIMM4DD.24, JSIMM5CC.24
R_MAINB1: JSIMM3EE.23, JSIMM4DD.23, JSIMM5CC.23
R_MAINB2: JSIMM3EE.22, JSIMM4DD.22, JSIMM5CC.22
R_MAINB3: JSIMM3EE.21, JSIMM4DD.21, JSIMM5CC.21
R_MAINB4: JSIMM3EE.20, JSIMM4DD.20, JSIMM5CC.20
R_MAINB5: JSIMM3EE.19, JSIMM4DD.19, JSIMM5CC.19
R_MAINB6: JSIMM3EE.18, JSIMM4DD.18, JSIMM5CC.18
R_MAINB7: JSIMM3EE.17, JSIMM4DD.17, JSIMM5CC.17
R_MAINB8: JSIMM3EE.16, JSIMM4DD.16, JSIMM5CC.16
R_MAINB9: JSIMM3EE.15, JSIMM4DD.15, JSIMM5CC.15
R_MAINB10: JSIMM3EE.14, JSIMM4DD.14, JSIMM5CC.14
R_MAINB11: JSIMM3EE.12, JSIMM4DD.12, JSIMM5CC.12
R_MAINB12: JSIMM3EE.11, JSIMM4DD.11, JSIMM5CC.11
R_MAINB13: JSIMM3EE.10, JSIMM4DD.10, JSIMM5CC.10
R_MAINB14: JSIMM3EE.9, JSIMM4DD.9, JSIMM5CC.9
R_MAINB15: JSIMM3EE.8, JSIMM4DD.8, JSIMM5CC.8
R_MAINB16: JSIMM3EE.7, JSIMM4DD.7, JSIMM5CC.7
R_MAINB17: JSIMM3EE.6, JSIMM4DD.6, JSIMM5CC.6
R_MAINB18: JSIMM3EE.5, JSIMM4DD.5, JSIMM5CC.5
R_MAINB19: JSIMM3EE.4, JSIMM4DD.4, JSIMM5CC.4
R_MAINB20: JSIMM3EE.3, JSIMM4DD.3, JSIMM5CC.3
SERVICE: JM1.R (SERVICE)
SPEAKER(+): JM1.10 (SPEAKER_(+))
SPEAKER(-): JM1.L (SPEAKER_(-))
SYNC: JM1.P (SYNC)
UK: JSIMM1EE.33, JSIMM2DD.33
VCC: JM1.3 (VDDA), JM1.4 (+5V), JM1.C (+5V), JM1.D (+5V), JSIMM1E.1, JSIMM1E.2, JSIMM2D.1, JSIMM2D.2, JSIMM3E.1, JSIMM3E.2, JSIMM4D.1, JSIMM4D.2, JSIMM5C.1, JSIMM5C.2, JSIMM6B.1, JSIMM6B.2
VSS: JM1.1 (GND), JM1.2 (VSSA), JM1.14 (VIDEO_GND), JM1.27 (GND), JM1.28 (GND), JM1.A (GND), JM1.B (GND), JM1.e (GND), JM1.f (GND), JSIMM1E.11, JSIMM1E.20, JSIMM1E.29, JSIMM1EE.13, JSIMM1EE.25, JSIMM1EE.32, JSIMM2D.11, JSIMM2D.20, JSIMM2D.29, JSIMM2DD.13, JSIMM2DD.25, JSIMM2DD.27, JSIMM2DD.32, JSIMM3E.11, JSIMM3E.20, JSIMM3E.29, JSIMM3EE.13, JSIMM3EE.25, JSIMM3EE.27, JSIMM3EE.32, JSIMM4D.11, JSIMM4D.20, JSIMM4D.29, JSIMM4DD.13, JSIMM4DD.25, JSIMM4DD.27, JSIMM4DD.32, JSIMM5C.11, JSIMM5C.20, JSIMM5C.29, JSIMM5CC.13, JSIMM5CC.25, JSIMM5CC.27, JSIMM5CC.32, JSIMM6B.11, JSIMM6B.20, JSIMM6B.29, JSIMM6BB.13, JSIMM6BB.25, JSIMM6BB.27, JSIMM6BB.32
~CEA: JSIMM6BB.28
~CEB: JSIMM6BB.29
~CEC: JSIMM6BB.30
~CED: JSIMM6BB.31
~CEE: JSIMM5CC.28
~CEF: JSIMM5CC.29
~CEG: JSIMM5CC.30
~CEH: JSIMM5CC.31
~CEI: JSIMM4DD.28
~CEJ: JSIMM4DD.29
~CEK: JSIMM4DD.30
~CEL: JSIMM4DD.31
~CEM: JSIMM3EE.28
~CEN: JSIMM3EE.29
~CEO: JSIMM3EE.30
~CEP: JSIMM3EE.31
~CE: JSIMM1EE.31, JSIMM2DD.31
~OEB: JSIMM6BB.35
~OEC: JSIMM5CC.35
~OED: JSIMM4DD.35
~OEE: JSIMM3EE.35
~OE: JSIMM1EE.35, JSIMM2DD.35
~RESET1: JSIMM6BB.26
~RESET2: JSIMM5CC.26
~RESET3: JSIMM4DD.26
~RESET4: JSIMM3EE.26
~RESET5: JSIMM1EE.26, JSIMM2DD.26
~WEB: JSIMM6BB.33
~WEC: JSIMM5CC.33
~WED: JSIMM4DD.33
~WEE: JSIMM3EE.33
~WE: JSIMM1EE.34, JSIMM2DD.34

Notes on the sheet:
[37..72]
REVISAR POSIBLE CORTO ENTRE VSS Y VCC
