jotego/jtcps/cores/cps3/sch/main.kicad_sch

## KiCad design cores/cps3/sch/main.kicad_sch (2022-10-26, an earlier design)

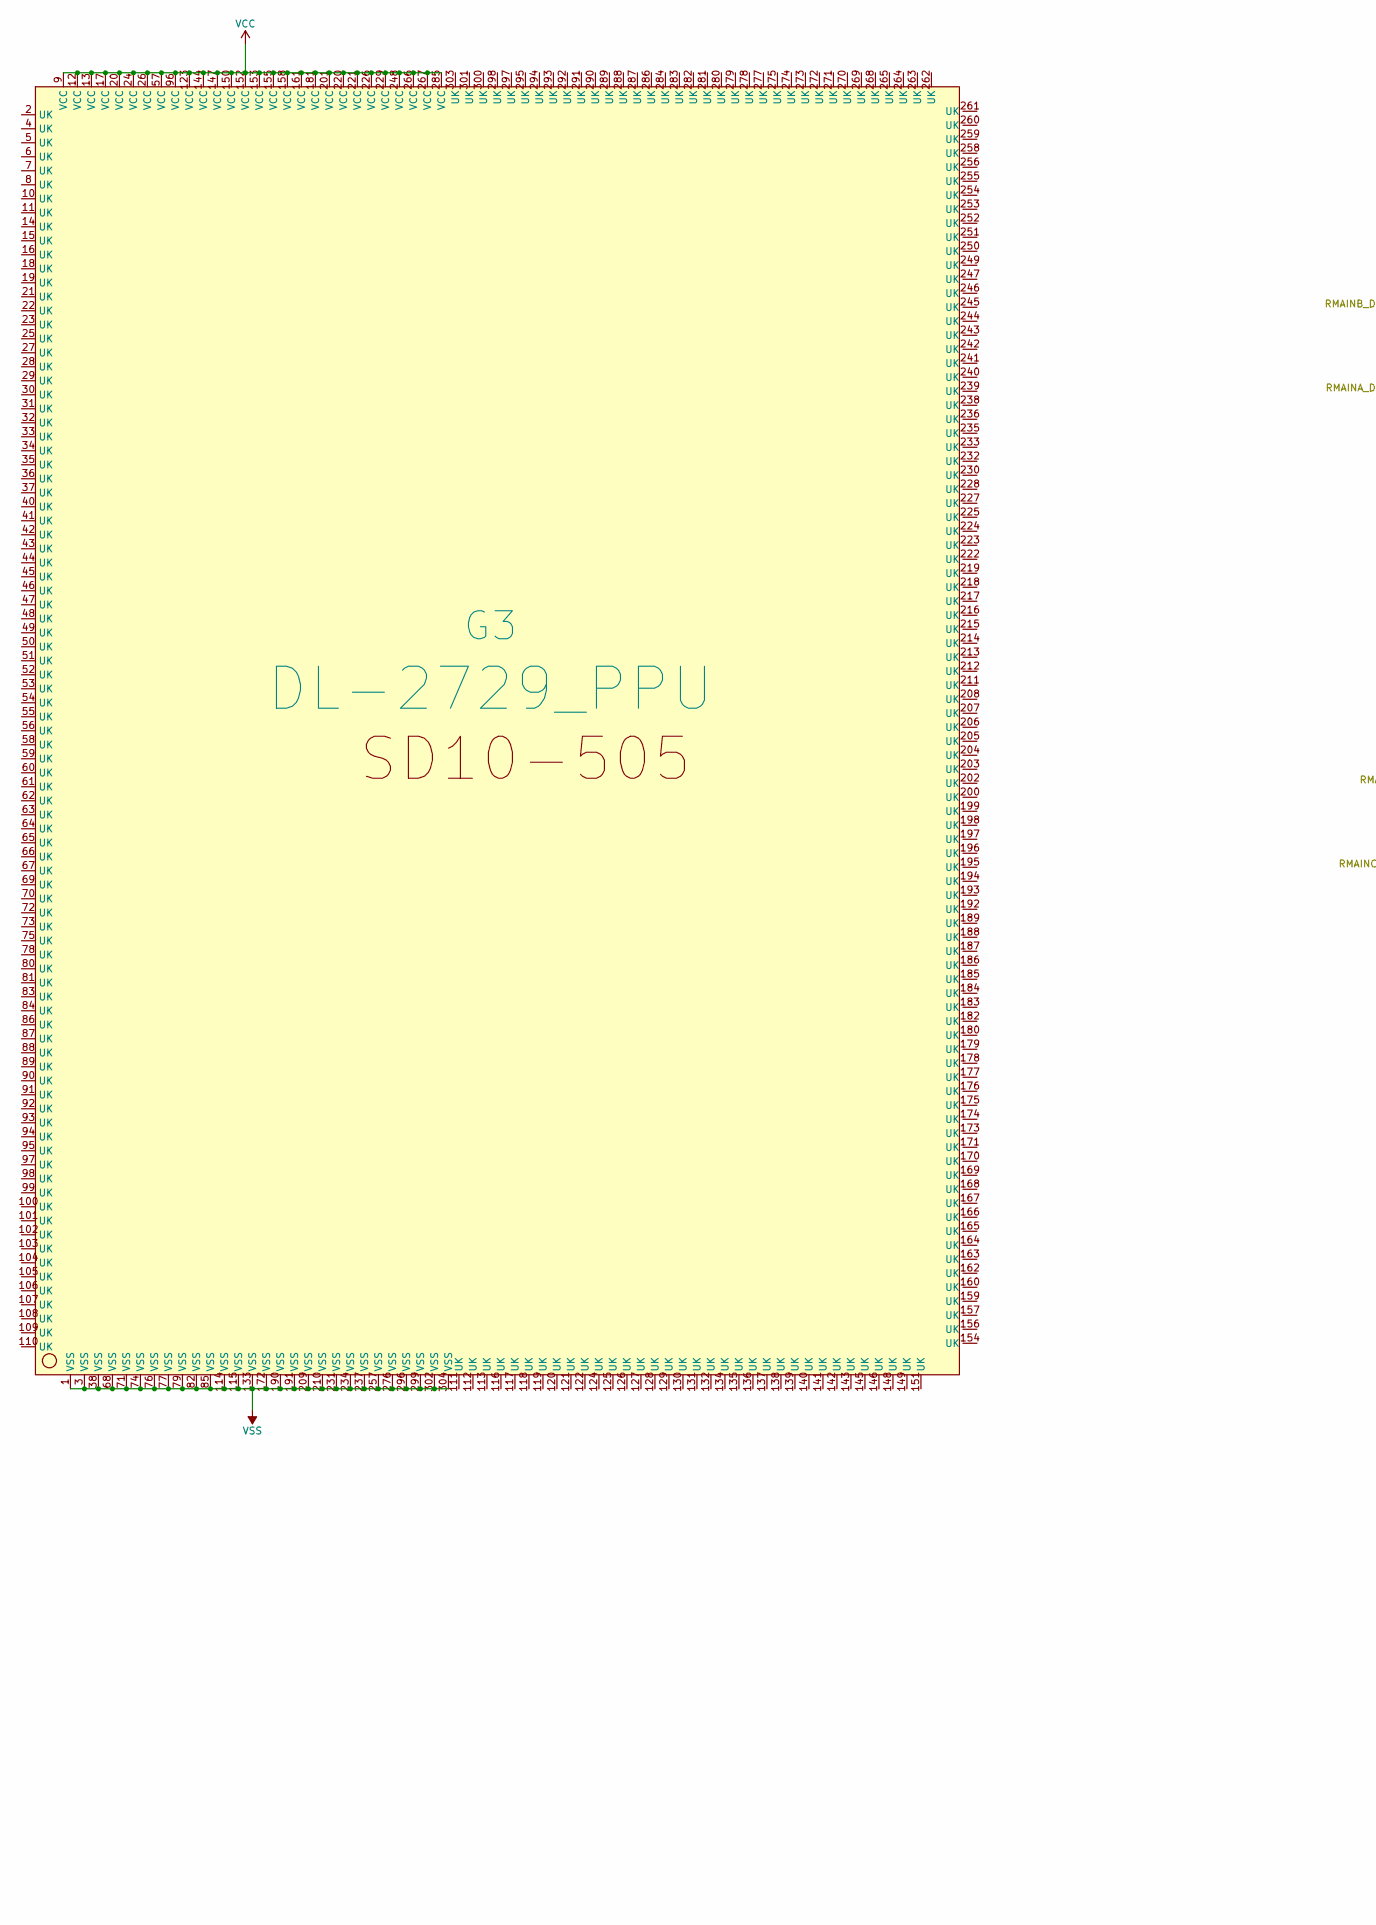
[picture p95: schematic main.kicad_sch, part in row 1, column 1]

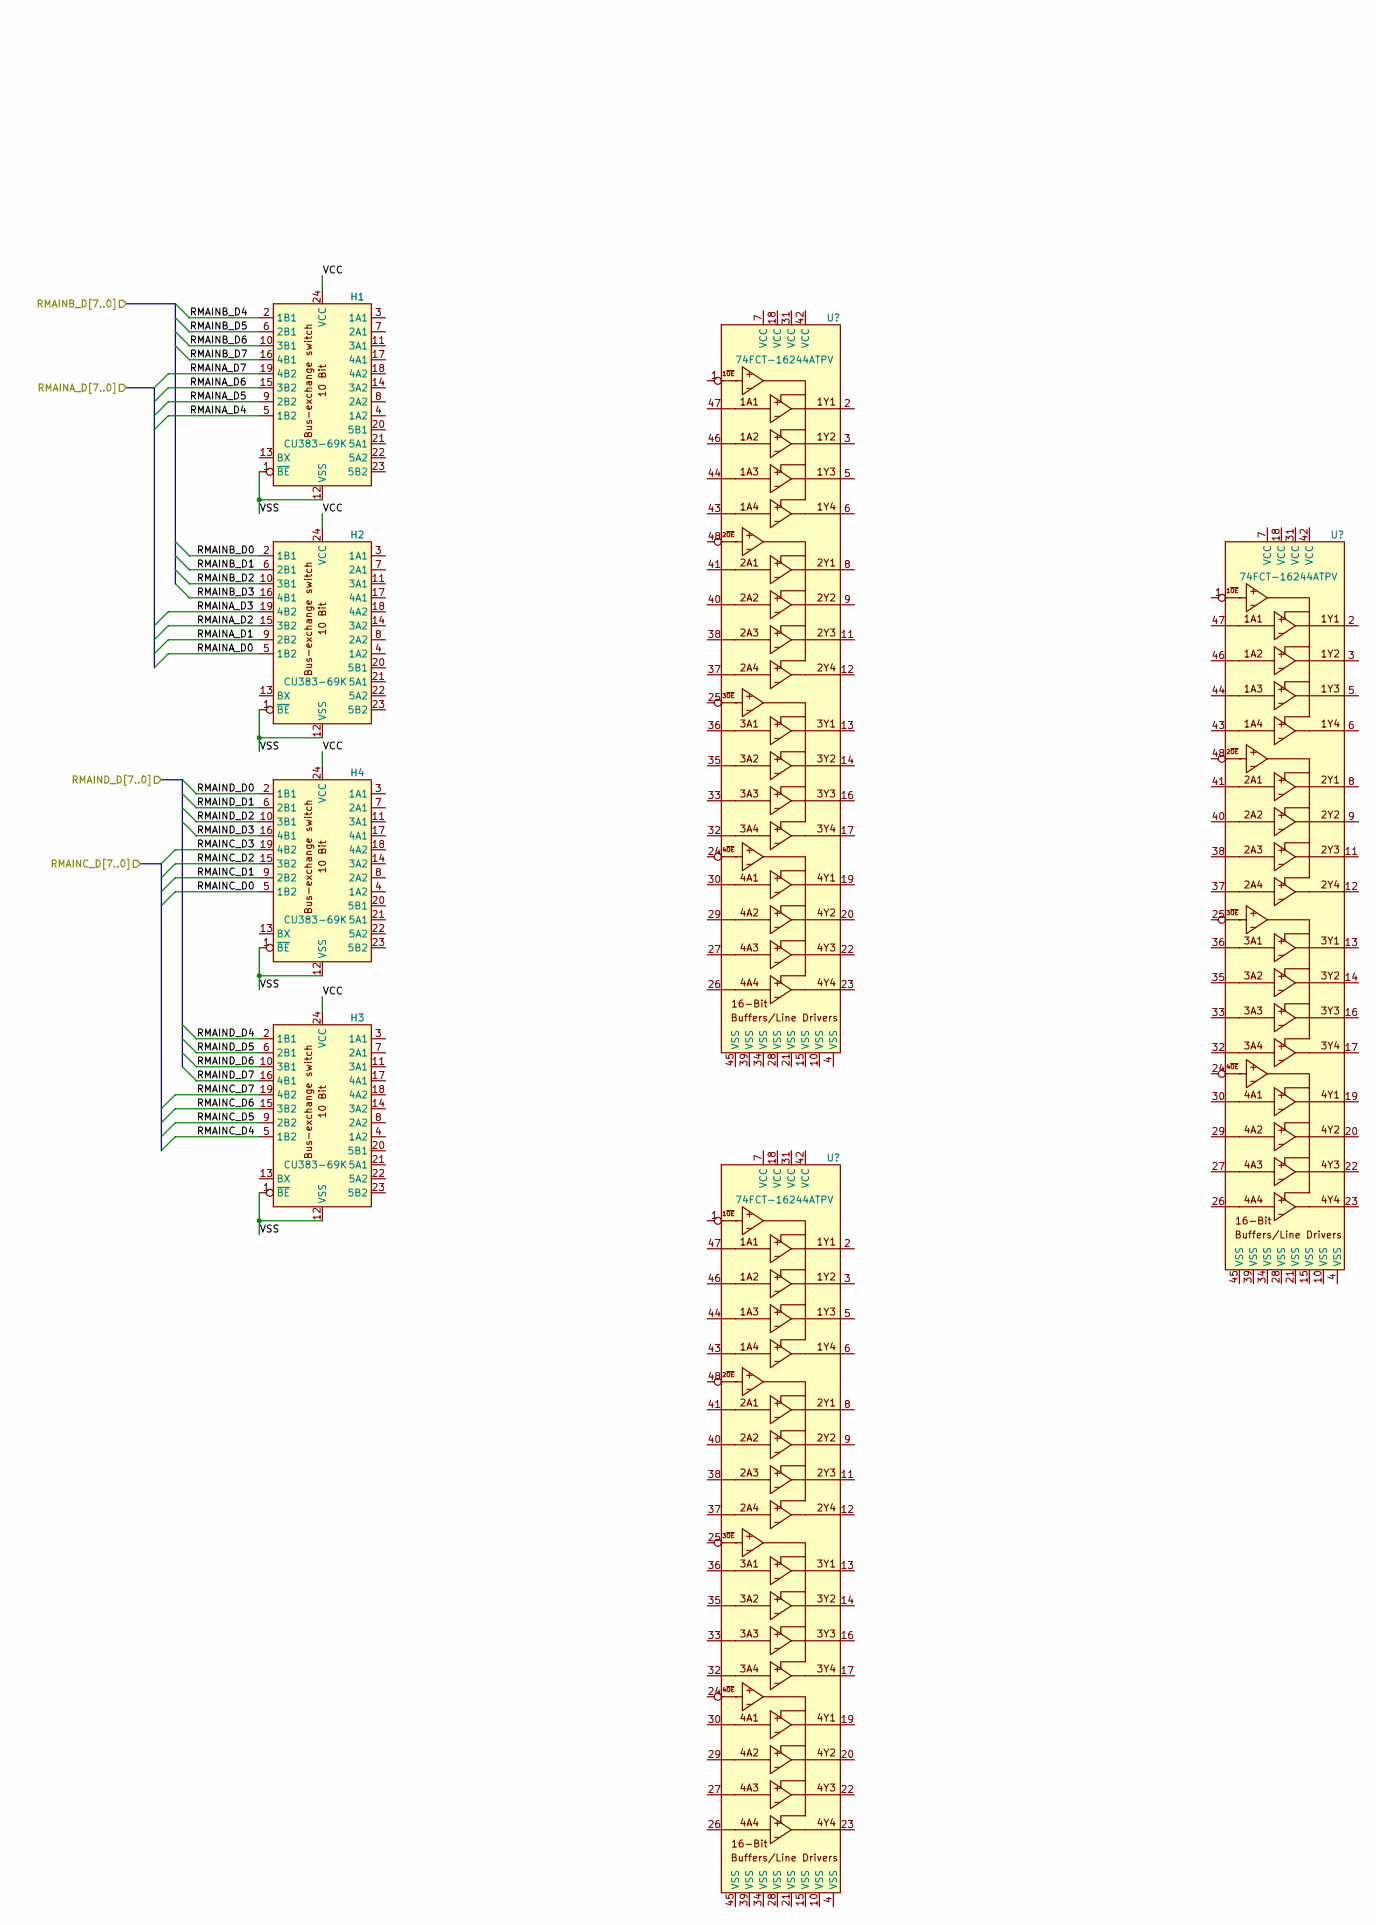
[picture p96: schematic main.kicad_sch, part in row 1, column 2]

Parts:
G3: DL-2729_PPU
H1, H2, H3, H4: CU383-69K

Connections:
unnamed: G3.1 (VSS), G3.3 (VSS), G3.38 (VSS), G3.68 (VSS), G3.71 (VSS), G3.74 (VSS), G3.76 (VSS), G3.77 (VSS), G3.79 (VSS), G3.82 (VSS), G3.85 (VSS), G3.114 (VSS), G3.115 (VSS), G3.133 (VSS), G3.172 (VSS), G3.190 (VSS), G3.191 (VSS), G3.209 (VSS), G3.210 (VSS), G3.231 (VSS), G3.234 (VSS), G3.237 (VSS), G3.257 (VSS), G3.276 (VSS), G3.296 (VSS), G3.299 (VSS), G3.302 (VSS), G3.304 (VSS)
unnamed: G3.9 (VCC), G3.12 (VCC), G3.13 (VCC), G3.17 (VCC), G3.20 (VCC), G3.24 (VCC), G3.26 (VCC), G3.57 (VCC), G3.96 (VCC), G3.123 (VCC), G3.144 (VCC), G3.147 (VCC), G3.150 (VCC), G3.152 (VCC), G3.153 (VCC), G3.155 (VCC), G3.158 (VCC), G3.161 (VCC), G3.181 (VCC), G3.201 (VCC), G3.220 (VCC), G3.221 (VCC), G3.226 (VCC), G3.229 (VCC), G3.248 (VCC), G3.266 (VCC), G3.267 (VCC), G3.285 (VCC)
RMAINA_D0: H2.5 (1B2)
RMAINA_D1: H2.9 (2B2)
RMAINA_D2: H2.15 (3B2)
RMAINA_D3: H2.19 (4B2)
RMAINA_D4: H1.5 (1B2)
RMAINA_D5: H1.9 (2B2)
RMAINA_D6: H1.15 (3B2)
RMAINA_D7: H1.19 (4B2)
RMAINB_D0: H2.2 (1B1)
RMAINB_D1: H2.6 (2B1)
RMAINB_D2: H2.10 (3B1)
RMAINB_D3: H2.16 (4B1)
RMAINB_D4: H1.2 (1B1)
RMAINB_D5: H1.6 (2B1)
RMAINB_D6: H1.10 (3B1)
RMAINB_D7: H1.16 (4B1)
RMAINC_D0: H4.5 (1B2)
RMAINC_D1: H4.9 (2B2)
RMAINC_D2: H4.15 (3B2)
RMAINC_D3: H4.19 (4B2)
RMAINC_D4: H3.5 (1B2)
RMAINC_D5: H3.9 (2B2)
RMAINC_D6: H3.15 (3B2)
RMAINC_D7: H3.19 (4B2)
RMAIND_D0: H4.2 (1B1)
RMAIND_D1: H4.6 (2B1)
RMAIND_D2: H4.10 (3B1)
RMAIND_D3: H4.16 (4B1)
RMAIND_D4: H3.2 (1B1)
RMAIND_D5: H3.6 (2B1)
RMAIND_D6: H3.10 (3B1)
RMAIND_D7: H3.16 (4B1)
VCC: H1.24 (VCC), H2.24 (VCC), H3.24 (VCC), H4.24 (VCC)
VSS: H1.1 (~BE), H1.12 (VSS), H2.1 (~BE), H2.12 (VSS), H3.1 (~BE), H3.12 (VSS), H4.1 (~BE), H4.12 (VSS)
