jotego/jtcps/cores/cps3/sch/ppu.kicad_sch

## KiCad design cores/cps3/sch/ppu.kicad_sch (2023-02-07, an earlier design)

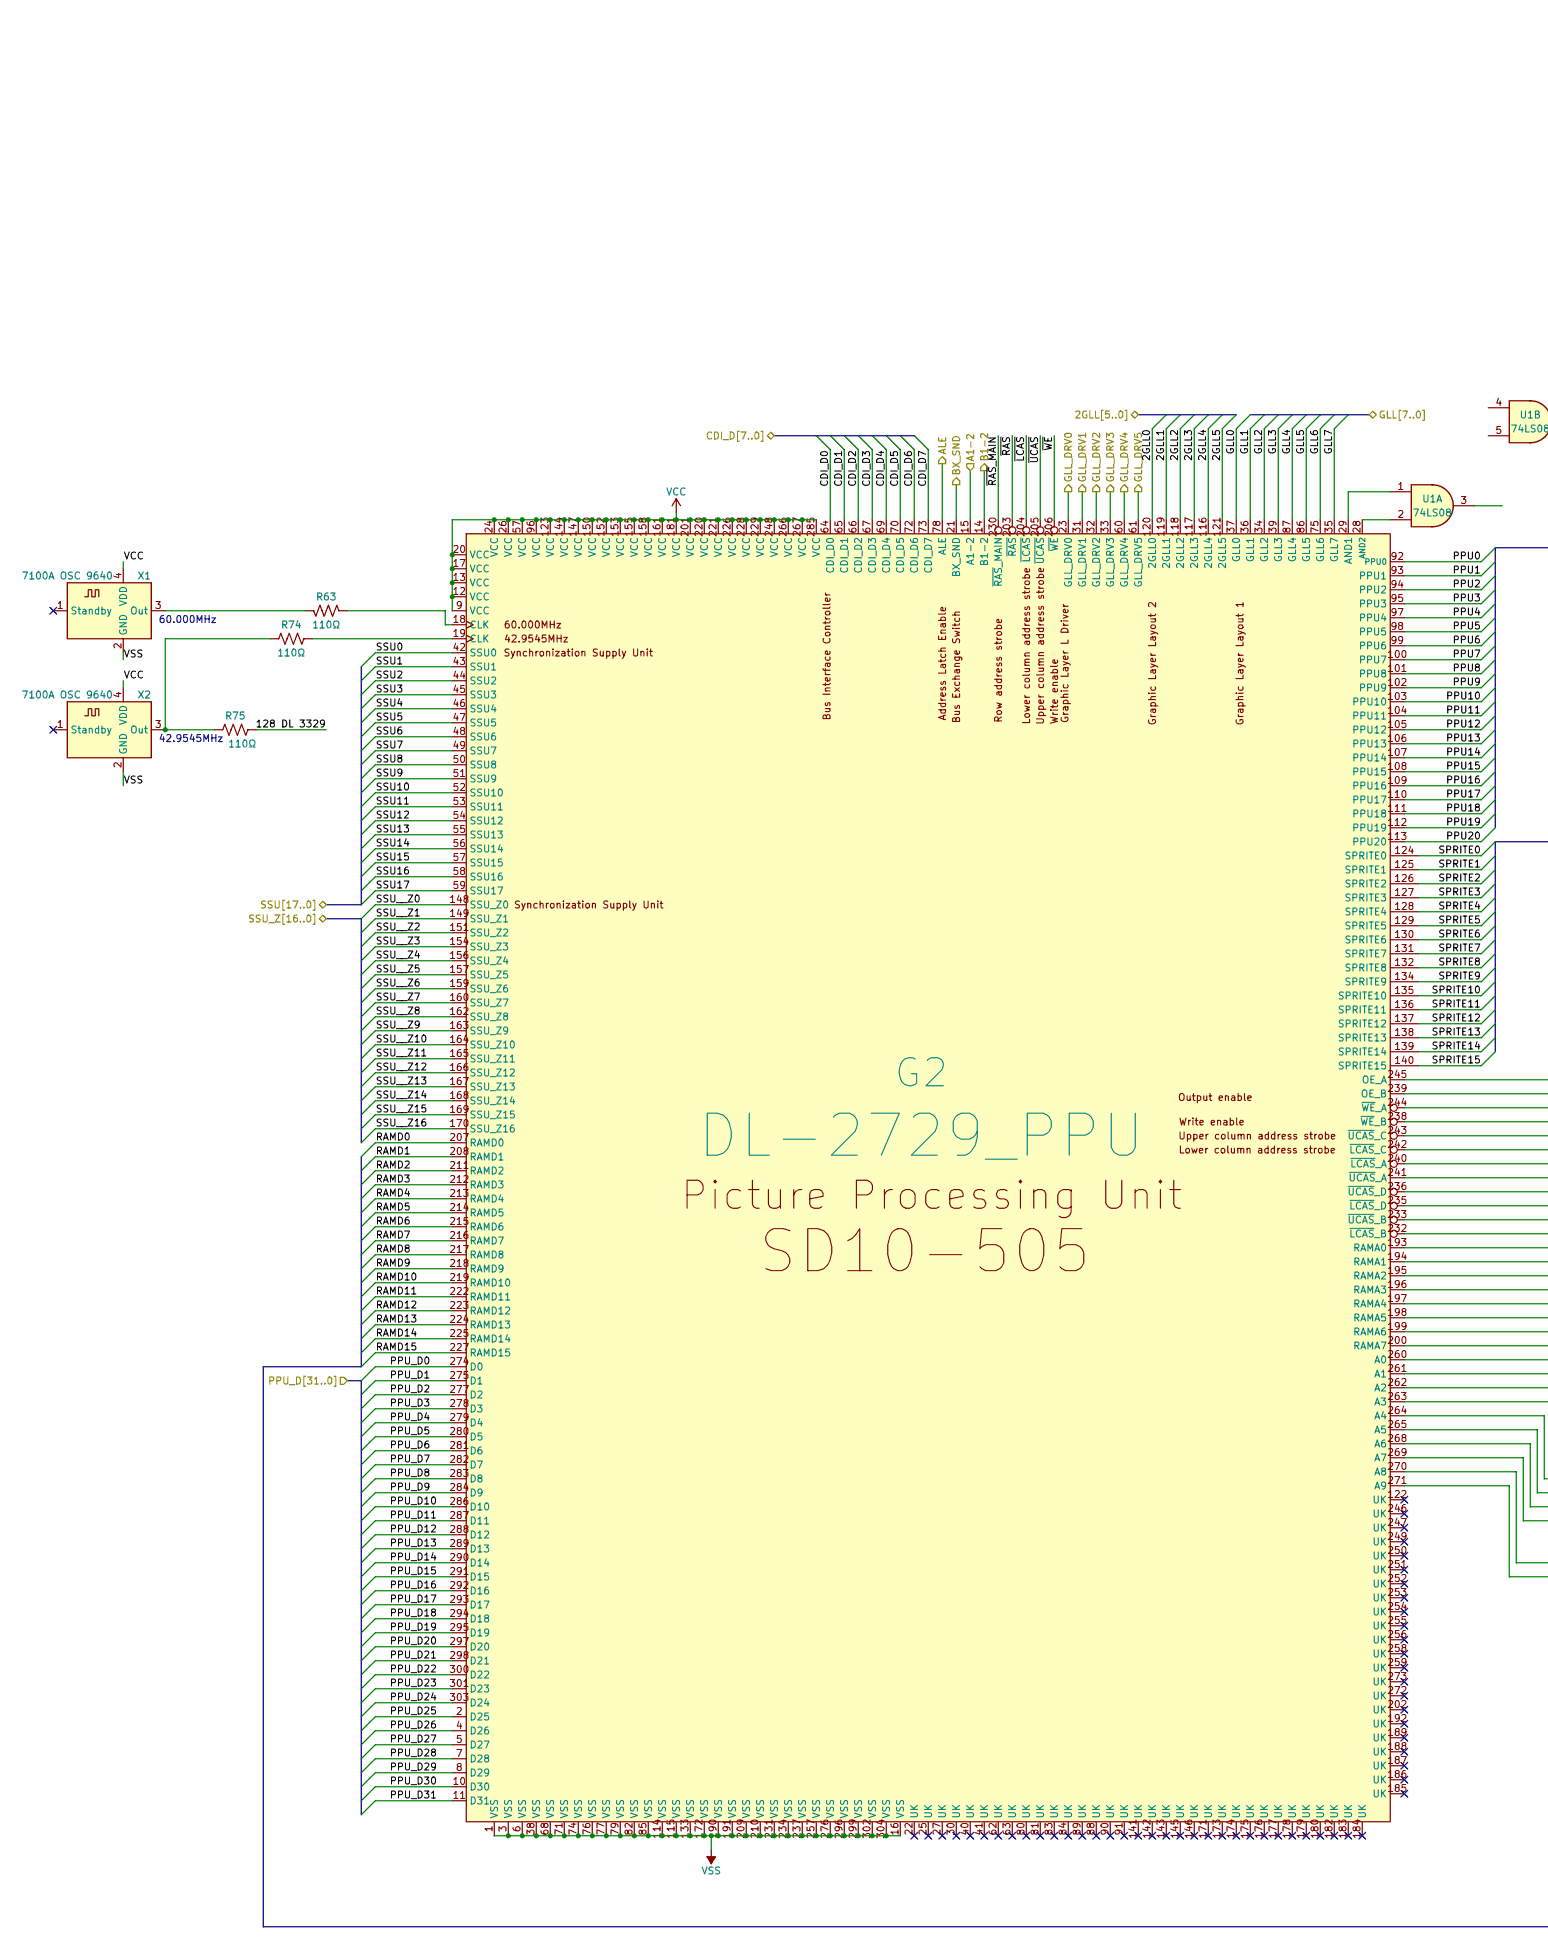
[picture p99: schematic ppu.kicad_sch, part in row 1, column 1]

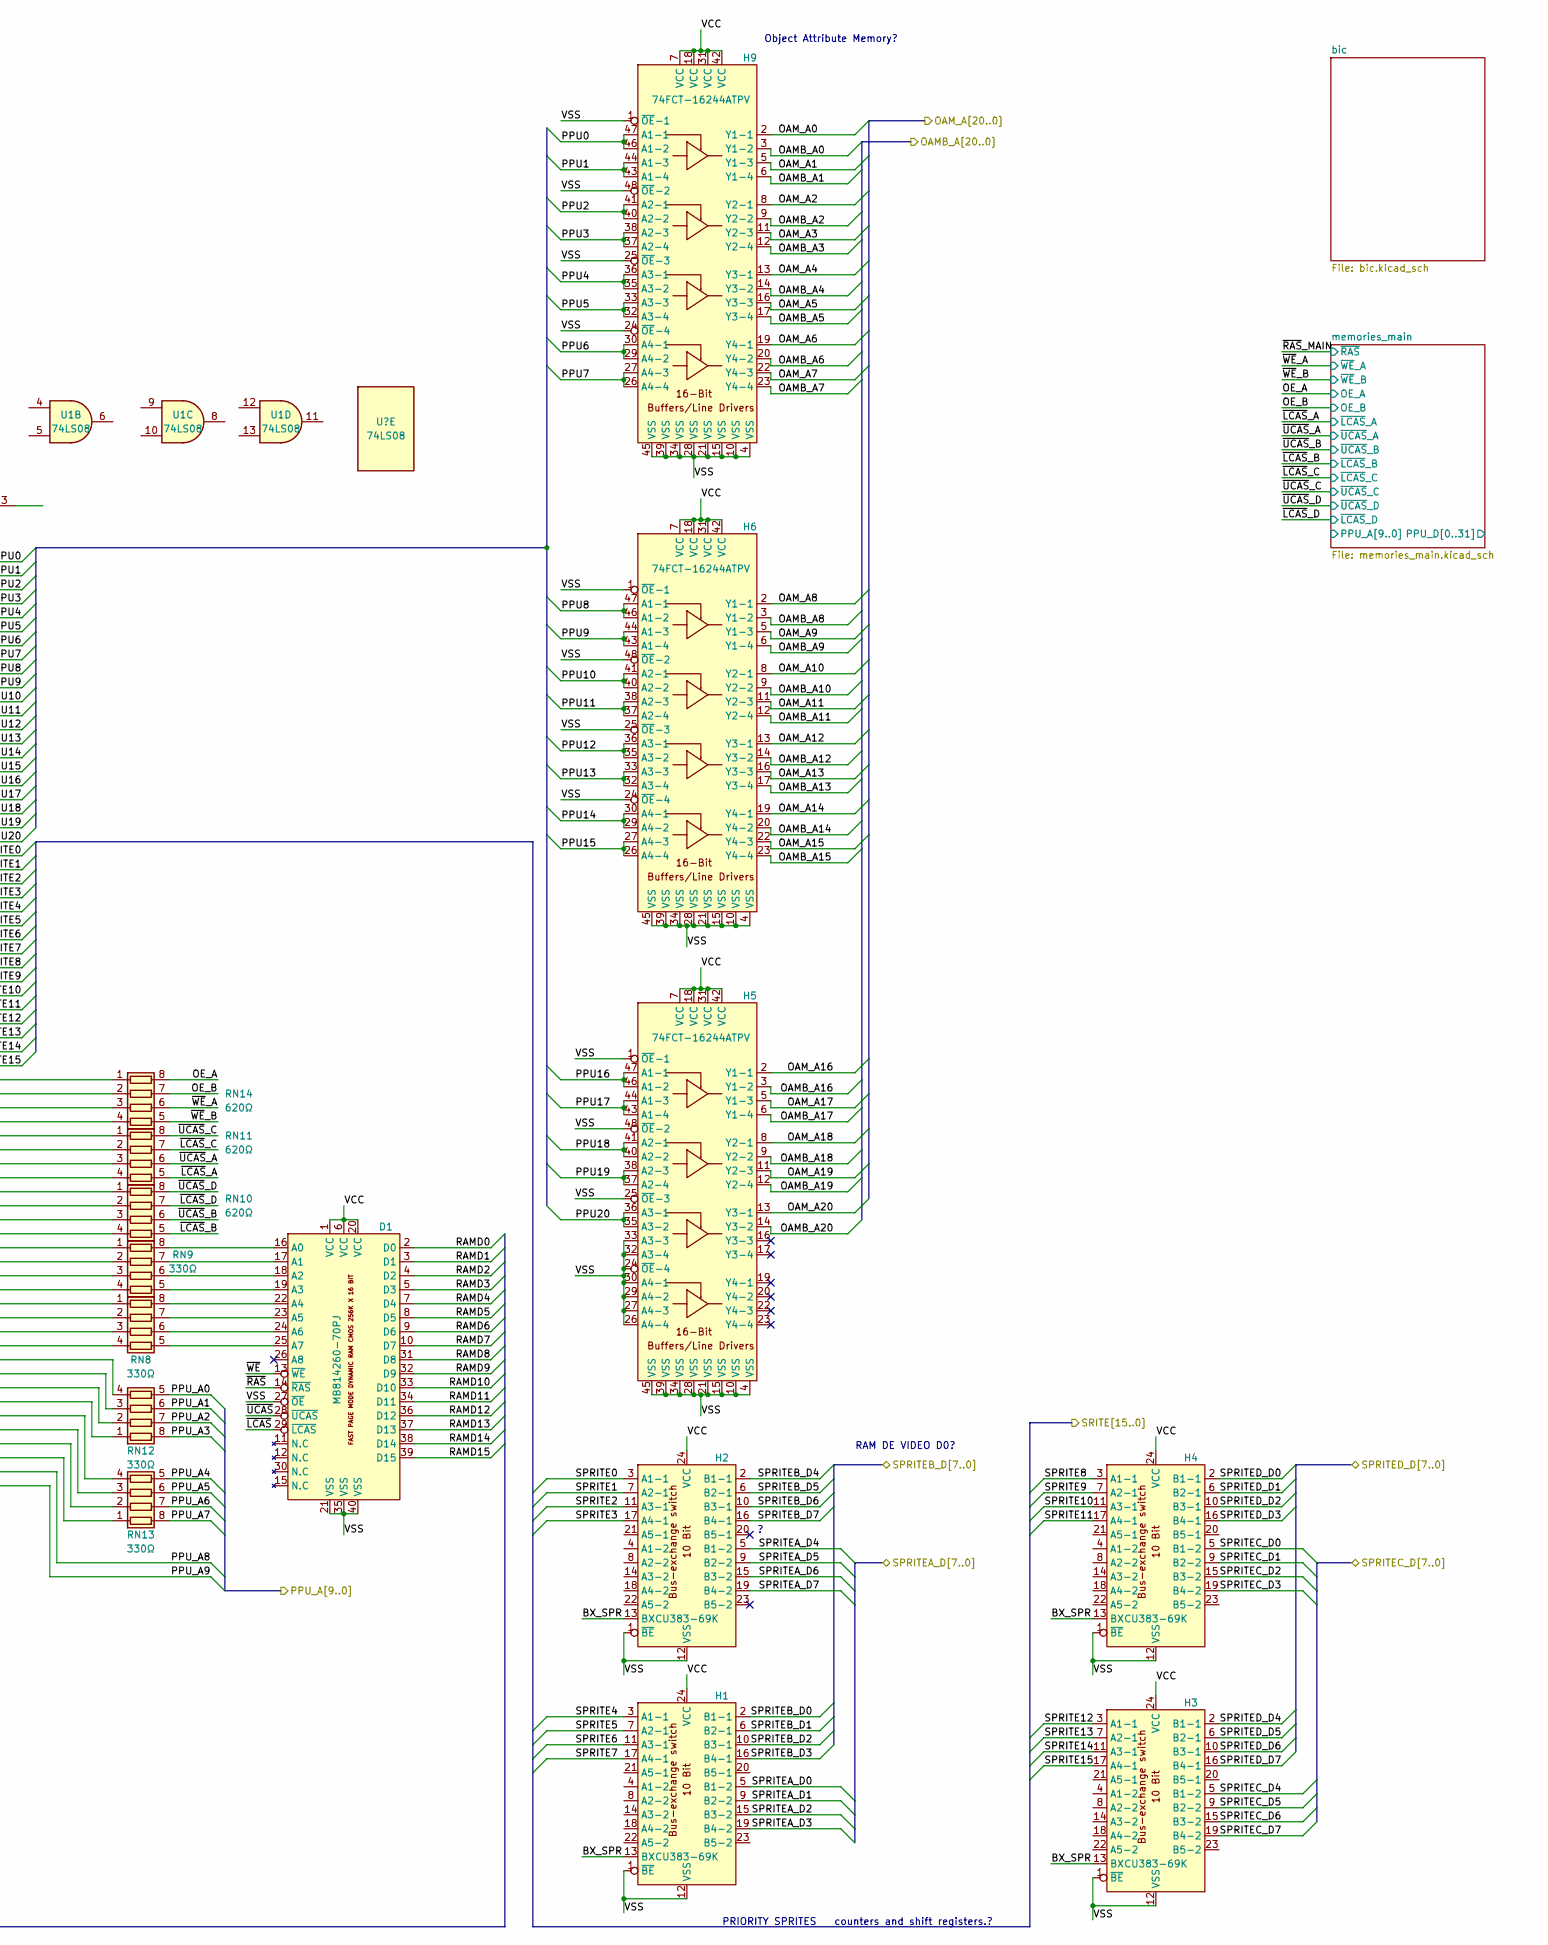
[picture p100: schematic ppu.kicad_sch, part in row 1, column 2]

Parts:
D1: MB814260-70PJ
G2: DL-2729_PPU
H1, H2, H3, H4: CU383-69K
H5, H6, H9: 74FCT-16244ATPV
R63, R74, R75: 110Ω
RN8, RN9, RN12, RN13: 330Ω
RN10, RN11, RN14: 620Ω
U1: 74LS08
X1, X2: 7100A OSC 9640; Oscillator_SMD_Abracon_ASDMB-4Pin_2.5x2.0mm

Connections:
2GLL0: G2.120 (2GLL0)
2GLL1: G2.119 (2GLL1)
2GLL2: G2.118 (2GLL2)
2GLL3: G2.117 (2GLL3)
2GLL4: G2.116 (2GLL4)
2GLL5: G2.121 (2GLL5)
A1-2: G2.15 (A1-2)
ALE: G2.78 (ALE)
B1-2: G2.14 (B1-2)
BX_SND: G2.21 (BX_SND)
BX_SPR: H1.13 (BX), H2.13 (BX), H3.13 (BX), H4.13 (BX)
CDI_D0: G2.64 (CDI_D0)
CDI_D1: G2.65 (CDI_D1)
CDI_D2: G2.66 (CDI_D2)
CDI_D3: G2.67 (CDI_D3)
CDI_D4: G2.69 (CDI_D4)
CDI_D5: G2.70 (CDI_D5)
CDI_D6: G2.72 (CDI_D6)
CDI_D7: G2.73 (CDI_D7)
DL 3329: R75.2
GLL0: G2.37 (GLL0)
GLL1: G2.36 (GLL1)
GLL2: G2.34 (GLL2)
GLL3: G2.39 (GLL3)
GLL4: G2.87 (GLL4)
GLL5: G2.86 (GLL5)
GLL6: G2.75 (GLL6)
GLL7: G2.35 (GLL7)
GLL_DRV0: G2.23 (GLL_DRV0)
GLL_DRV1: G2.31 (GLL_DRV1)
GLL_DRV2: G2.32 (GLL_DRV2)
GLL_DRV3: G2.33 (GLL_DRV3)
GLL_DRV4: G2.60 (GLL_DRV4)
GLL_DRV5: G2.61 (GLL_DRV5)
unnamed: D1.16 (A0), RN9.8 (R1.2)
unnamed: D1.17 (A1), RN9.7 (R2.2)
unnamed: D1.18 (A2), RN9.6 (R3.2)
unnamed: D1.19 (A3), RN9.5 (R4.2)
unnamed: D1.22 (A4), RN8.8 (R1.2)
unnamed: D1.23 (A5), RN8.7 (R2.2)
unnamed: D1.24 (A6), RN8.6 (R3.2)
unnamed: D1.25 (A7), RN8.5 (R4.2)
unnamed: G2.1 (VSS), G2.3 (VSS), G2.6 (VSS), G2.16 (VSS), G2.38 (VSS), G2.68 (VSS), G2.71 (VSS), G2.74 (VSS), G2.76 (VSS), G2.77 (VSS), G2.79 (VSS), G2.82 (VSS), G2.85 (VSS), G2.114 (VSS), G2.115 (VSS), G2.133 (VSS), G2.172 (VSS), G2.190 (VSS), G2.191 (VSS), G2.209 (VSS), G2.210 (VSS), G2.231 (VSS), G2.234 (VSS), G2.237 (VSS), G2.257 (VSS), G2.276 (VSS), G2.296 (VSS), G2.299 (VSS), G2.302 (VSS), G2.304 (VSS)
unnamed: G2.9 (VCC), G2.12 (VCC), G2.13 (VCC), G2.17 (VCC), G2.20 (VCC), G2.24 (VCC), G2.26 (VCC), G2.57 (SSU15), G2.96 (VCC), G2.123 (VCC), G2.144 (VCC), G2.147 (VCC), G2.150 (VCC), G2.152 (VCC), G2.153 (VCC), G2.155 (VCC), G2.158 (VCC), G2.161 (VCC), G2.181 (VCC), G2.201 (VCC), G2.220 (VCC), G2.221 (VCC), G2.226 (VCC), G2.228 (VCC), G2.229 (VCC), G2.248 (VCC), G2.266 (VCC), G2.267 (VCC), G2.285 (VCC)
unnamed: G2.18 (CLK), R63.2
unnamed: G2.19 (CLK), R74.2
unnamed: G2.28 (AND2), U1.2
unnamed: G2.29 (AND1), U1.1
unnamed: G2.193 (RAMA0), RN9.1 (R1.1)
unnamed: G2.194 (RAMA1), RN9.2 (R2.1)
unnamed: G2.195 (RAMA2), RN9.3 (R3.1)
unnamed: G2.196 (RAMA3), RN9.4 (R4.1)
unnamed: G2.197 (RAMA4), RN8.1 (R1.1)
unnamed: G2.198 (RAMA5), RN8.2 (R2.1)
unnamed: G2.199 (RAMA6), RN8.3 (R3.1)
unnamed: G2.200 (RAMA7), RN8.4 (R4.1)
unnamed: G2.232 (~LCAS_B), RN10.4 (R4.1)
unnamed: G2.233 (~UCAS_B), RN10.3 (R3.1)
unnamed: G2.235 (~LCAS_D), RN10.2 (R2.1)
unnamed: G2.236 (~UCAS_D), RN10.1 (R1.1)
unnamed: G2.238 (~WE_B), RN14.4 (R4.1)
unnamed: G2.239 (OE_B), RN14.2 (R2.1)
unnamed: G2.240 (~LCAS_A), RN11.3 (R3.1)
unnamed: G2.241 (~UCAS_A), RN11.4 (R4.1)
unnamed: G2.242 (~LCAS_C), RN11.2 (R2.1)
unnamed: G2.243 (~UCAS_C), RN11.1 (R1.1)
unnamed: G2.244 (~WE_A), RN14.3 (R3.1)
unnamed: G2.245 (OE_A), RN14.1 (R1.1)
unnamed: G2.260 (A0), RN12.4 (R4.1)
unnamed: G2.261 (A1), RN12.3 (R3.1)
unnamed: G2.262 (A2), RN12.2 (R2.1)
unnamed: G2.263 (A3), RN12.1 (R1.1)
unnamed: G2.264 (A4), RN13.4 (R4.1)
unnamed: G2.265 (A5), RN13.3 (R3.1)
unnamed: G2.268 (A6), RN13.2 (R2.1)
unnamed: G2.269 (A7), RN13.1 (R1.1)
unnamed: R63.1, X1.3 (Out)
unnamed: R74.1, R75.1, X2.3 (Out)
OAMB_A0: H9.3 (Y1-2)
OAMB_A1: H9.6 (Y1-4)
OAMB_A2: H9.9 (Y2-2)
OAMB_A3: H9.12 (Y2-4)
OAMB_A4: H9.14 (Y3-2)
OAMB_A5: H9.17 (Y3-4)
OAMB_A6: H9.20 (Y4-2)
OAMB_A7: H9.23 (Y4-4)
OAMB_A8: H6.3 (Y1-2)
OAMB_A9: H6.6 (Y1-4)
OAMB_A10: H6.9 (Y2-2)
OAMB_A11: H6.12 (Y2-4)
OAMB_A12: H6.14 (Y3-2)
OAMB_A13: H6.17 (Y3-4)
OAMB_A14: H6.20 (Y4-2)
OAMB_A15: H6.23 (Y4-4)
OAMB_A16: H5.3 (Y1-2)
OAMB_A17: H5.6 (Y1-4)
OAMB_A18: H5.9 (Y2-2)
OAMB_A19: H5.12 (Y2-4)
OAMB_A20: H5.14 (Y3-2)
OAM_A0: H9.2 (Y1-1)
OAM_A1: H9.5 (Y1-3)
OAM_A2: H9.8 (Y2-1)
OAM_A3: H9.11 (Y2-3)
OAM_A4: H9.13 (Y3-1)
OAM_A5: H9.16 (Y3-3)
OAM_A6: H9.19 (Y4-1)
OAM_A7: H9.22 (Y4-3)
OAM_A8: H6.2 (Y1-1)
OAM_A9: H6.5 (Y1-3)
OAM_A10: H6.8 (Y2-1)
OAM_A11: H6.11 (Y2-3)
OAM_A12: H6.13 (Y3-1)
OAM_A13: H6.16 (Y3-3)
OAM_A14: H6.19 (Y4-1)
OAM_A15: H6.22 (Y4-3)
OAM_A16: H5.2 (Y1-1)
OAM_A17: H5.5 (Y1-3)
OAM_A18: H5.8 (Y2-1)
OAM_A19: H5.11 (Y2-3)
OAM_A20: H5.13 (Y3-1)
OE_A: RN14.8 (R1.2)
OE_B: RN14.7 (R2.2)
PPU0: G2.92 (PPU0), H9.46 (A1-2), H9.47 (A1-1)
PPU1: G2.93 (PPU1), H9.43 (A1-4), H9.44 (A1-3)
PPU2: G2.94 (PPU2), H9.40 (A2-2), H9.41 (A2-1)
PPU3: G2.95 (PPU3), H9.37 (A2-4), H9.38 (A2-3)
PPU4: G2.97 (PPU4), H9.35 (A3-2), H9.36 (A3-1)
PPU5: G2.98 (PPU5), H9.32 (A3-4), H9.33 (A3-3)
PPU6: G2.99 (PPU6), H9.29 (A4-2), H9.30 (A4-1)
PPU7: G2.100 (PPU7), H9.26 (A4-4), H9.27 (A4-3)
PPU8: G2.101 (PPU8), H6.46 (A1-2), H6.47 (A1-1)
PPU9: G2.102 (PPU9), H6.43 (A1-4), H6.44 (A1-3)
PPU10: G2.103 (PPU10), H6.40 (A2-2), H6.41 (A2-1)
PPU11: G2.104 (PPU11), H6.37 (A2-4), H6.38 (A2-3)
PPU12: G2.105 (PPU12), H6.35 (A3-2), H6.36 (A3-1)
PPU13: G2.106 (PPU13), H6.32 (A3-4), H6.33 (A3-3)
PPU14: G2.107 (PPU14), H6.29 (A4-2), H6.30 (A4-1)
PPU15: G2.108 (PPU15), H6.26 (A4-4), H6.27 (A4-3)
PPU16: G2.109 (PPU16), H5.46 (A1-2), H5.47 (A1-1)
PPU17: G2.110 (PPU17), H5.43 (A1-4), H5.44 (A1-3)
PPU18: G2.111 (PPU18), H5.40 (A2-2), H5.41 (A2-1)
PPU19: G2.112 (PPU19), H5.37 (A2-4), H5.38 (A2-3)
PPU20: G2.113 (PPU20), H5.35 (A3-2), H5.36 (A3-1)
PPU_A0: RN12.5 (R4.2)
PPU_A1: RN12.6 (R3.2)
PPU_A2: RN12.7 (R2.2)
PPU_A3: RN12.8 (R1.2)
PPU_A4: RN13.5 (R4.2)
PPU_A5: RN13.6 (R3.2)
PPU_A6: RN13.7 (R2.2)
PPU_A7: RN13.8 (R1.2)
PPU_A8: G2.270 (A8)
PPU_A9: G2.271 (A9)
PPU_D0: G2.274 (D0)
PPU_D1: G2.275 (D1)
PPU_D2: G2.277 (D2)
PPU_D3: G2.278 (D3)
PPU_D4: G2.279 (D4)
PPU_D5: G2.280 (D5)
PPU_D6: G2.281 (D6)
PPU_D7: G2.282 (D7)
PPU_D8: G2.283 (D8)
PPU_D9: G2.284 (D9)
PPU_D10: G2.286 (D10)
PPU_D11: G2.287 (D11)
PPU_D12: G2.288 (D12)
PPU_D13: G2.289 (D13)
PPU_D14: G2.290 (D14)
PPU_D15: G2.291 (D15)
PPU_D16: G2.292 (D16)
PPU_D17: G2.293 (D17)
PPU_D18: G2.294 (D18)
PPU_D19: G2.295 (D19)
PPU_D20: G2.297 (D20)
PPU_D21: G2.298 (D21)
PPU_D22: G2.300 (D22)
PPU_D23: G2.301 (D23)
PPU_D24: G2.303 (D24)
PPU_D25: G2.2 (D25)
PPU_D26: G2.4 (D26)
PPU_D27: G2.5 (D27)
PPU_D28: G2.7 (D28)
PPU_D29: G2.8 (D29)
PPU_D30: G2.10 (D30)
PPU_D31: G2.11 (D31)
RAMD0: D1.2 (D0), G2.207 (RAMD0)
RAMD1: D1.3 (D1), G2.208 (RAMD1)
RAMD2: D1.4 (D2), G2.211 (RAMD2)
RAMD3: D1.5 (D3), G2.212 (RAMD3)
RAMD4: D1.7 (D4), G2.213 (RAMD4)
RAMD5: D1.8 (D5), G2.214 (RAMD5)
RAMD6: D1.9 (D6), G2.215 (RAMD6)
RAMD7: D1.10 (D7), G2.216 (RAMD7)
RAMD8: D1.31 (D8), G2.217 (RAMD8)
RAMD9: D1.32 (D9), G2.218 (RAMD9)
RAMD10: D1.33 (D10), G2.219 (RAMD10)
RAMD11: D1.34 (D11), G2.222 (RAMD11)
RAMD12: D1.36 (D12), G2.223 (RAMD12)
RAMD13: D1.37 (D13), G2.224 (RAMD13)
RAMD14: D1.38 (D14), G2.225 (RAMD14)
RAMD15: D1.39 (D15), G2.227 (RAMD15)
SPRITE0: G2.124 (SPRITE0), H2.3 (A1-1)
SPRITE1: G2.125 (SPRITE1), H2.7 (A2-1)
SPRITE2: G2.126 (SPRITE2), H2.11 (A3-1)
SPRITE3: G2.127 (SPRITE3), H2.17 (A4-1)
SPRITE4: G2.128 (SPRITE4), H1.3 (A1-1)
SPRITE5: G2.129 (SPRITE5), H1.7 (A2-1)
SPRITE6: G2.130 (SPRITE6), H1.11 (A3-1)
SPRITE7: G2.131 (SPRITE7), H1.17 (A4-1)
SPRITE8: G2.132 (SPRITE8), H4.3 (A1-1)
SPRITE9: G2.134 (SPRITE9), H4.7 (A2-1)
SPRITE10: G2.135 (SPRITE10), H4.11 (A3-1)
SPRITE11: G2.136 (SPRITE11), H4.17 (A4-1)
SPRITE12: G2.137 (SPRITE12), H3.3 (A1-1)
SPRITE13: G2.138 (SPRITE13), H3.7 (A2-1)
SPRITE14: G2.139 (SPRITE14), H3.11 (A3-1)
SPRITE15: G2.140 (SPRITE15), H3.17 (A4-1)
SPRITEA_D0: H1.5 (B1-2)
SPRITEA_D1: H1.9 (B2-2)
SPRITEA_D2: H1.15 (B3-2)
SPRITEA_D3: H1.19 (B4-2)
SPRITEA_D4: H2.5 (B1-2)
SPRITEA_D5: H2.9 (B2-2)
SPRITEA_D6: H2.15 (B3-2)
SPRITEA_D7: H2.19 (B4-2)
SPRITEB_D0: H1.2 (B1-1)
SPRITEB_D1: H1.6 (B2-1)
SPRITEB_D2: H1.10 (B3-1)
SPRITEB_D3: H1.16 (B4-1)
SPRITEB_D4: H2.2 (B1-1)
SPRITEB_D5: H2.6 (B2-1)
SPRITEB_D6: H2.10 (B3-1)
SPRITEB_D7: H2.16 (B4-1)
SPRITEC_D0: H4.5 (B1-2)
SPRITEC_D1: H4.9 (B2-2)
SPRITEC_D2: H4.15 (B3-2)
SPRITEC_D3: H4.19 (B4-2)
SPRITEC_D4: H3.5 (B1-2)
SPRITEC_D5: H3.9 (B2-2)
SPRITEC_D6: H3.15 (B3-2)
SPRITEC_D7: H3.19 (B4-2)
SPRITED_D0: H4.2 (B1-1)
SPRITED_D1: H4.6 (B2-1)
SPRITED_D2: H4.10 (B3-1)
SPRITED_D3: H4.16 (B4-1)
SPRITED_D4: H3.2 (B1-1)
SPRITED_D5: H3.6 (B2-1)
SPRITED_D6: H3.10 (B3-1)
SPRITED_D7: H3.16 (B4-1)
SSU0: G2.42 (SSU0)
SSU1: G2.43 (SSU1)
SSU2: G2.44 (SSU2)
SSU3: G2.45 (SSU3)
SSU4: G2.46 (SSU4)
SSU5: G2.47 (SSU5)
SSU6: G2.48 (SSU6)
SSU7: G2.49 (SSU7)
SSU8: G2.50 (SSU8)
SSU9: G2.51 (SSU9)
SSU10: G2.52 (SSU10)
SSU11: G2.53 (SSU11)
SSU12: G2.54 (SSU12)
SSU13: G2.55 (SSU13)
SSU14: G2.56 (SSU14)
SSU15: G2.57 (SSU15)
SSU16: G2.58 (SSU16)
SSU17: G2.59 (SSU17)
SSU__Z0: G2.148 (SSU_Z0)
SSU__Z1: G2., G2.149 (SSU_Z1)
SSU__Z2: G2.151 (SSU_Z2)
SSU__Z3: G2.154 (SSU_Z3)
SSU__Z4: G2.156 (SSU_Z4)
SSU__Z5: G2.157 (SSU_Z5)
SSU__Z6: G2.159 (SSU_Z6)
SSU__Z7: G2.160 (SSU_Z7)
SSU__Z8: G2.162 (SSU_Z8)
SSU__Z9: G2.163 (SSU_Z9)
SSU__Z10: G2.164 (SSU_Z10)
SSU__Z11: G2.165 (SSU_Z11)
SSU__Z12: G2.166 (SSU_Z12)
SSU__Z13: G2.167 (SSU_Z13)
SSU__Z14: G2.168 (SSU_Z14)
SSU__Z15: G2.169 (SSU_Z15)
SSU__Z16: G2.170 (SSU_Z16)
VCC: D1.1 (VCC), D1.6 (VCC), D1.20 (VCC), H1.24 (VCC), H2.24 (VCC), H3.24 (VCC), H4.24 (VCC), H5.7 (VCC), H5.18 (VCC), H5.31 (VCC), H5.42 (VCC), H6.7 (VCC), H6.18 (VCC), H6.31 (VCC), H6.42 (VCC), H9.7 (VCC), H9.18 (VCC), H9.31 (VCC), H9.42 (VCC), X1.4 (VDD), X2.4 (VDD)
VSS: D1.21 (VSS), D1.27 (~OE), D1.35 (VSS), D1.40 (VSS), H1.1 (~BE), H1.12 (VSS), H2.1 (~BE), H2.12 (VSS), H3.1 (~BE), H3.12 (VSS), H4.1 (~BE), H4.12 (VSS), H5.1 (~OE-1), H5.4 (VSS), H5.10 (VSS), H5.15 (VSS), H5.21 (VSS), H5.24 (~OE-4), H5.25 (~OE-3), H5.26 (A4-4), H5.27 (A4-3), H5.28 (VSS), H5.29 (A4-2), H5.30 (A4-1), H5.32 (A3-4), H5.33 (A3-3), H5.34 (VSS), H5.39 (VSS), H5.45 (VSS), H5.48 (~OE-2), H6.1 (~OE-1), H6.4 (VSS), H6.10 (VSS), H6.15 (VSS), H6.21 (VSS), H6.24 (~OE-4), H6.25 (~OE-3), H6.28 (VSS), H6.34 (VSS), H6.39 (VSS), H6.45 (VSS), H6.48 (~OE-2), H9.1 (~OE-1), H9.4 (VSS), H9.10 (VSS), H9.15 (VSS), H9.21 (VSS), H9.24 (~OE-4), H9.25 (~OE-3), H9.28 (VSS), H9.34 (VSS), H9.39 (VSS), H9.45 (VSS), H9.48 (~OE-2), X1.2 (GND), X2.2 (GND)
~LCAS: D1.29 (~LCAS), G2.204 (~LCAS)
~LCAS_A: RN11.5 (R4.2)
~LCAS_B: RN10.5 (R4.2)
~LCAS_C: RN11.7 (R2.2)
~LCAS_D: RN10.7 (R2.2)
~RAS: D1.14 (~RAS), G2.203 (~RAS)
~RAS_MAIN: G2.230 (~RAS_MAIN)
~UCAS: D1.28 (~UCAS), G2.205 (~UCAS)
~UCAS_A: RN11.6 (R3.2)
~UCAS_B: RN10.6 (R3.2)
~UCAS_C: RN11.8 (R1.2)
~UCAS_D: RN10.8 (R1.2)
~WE: D1.13 (~WE), G2.206 (~WE)
~WE_A: RN14.6 (R3.2)
~WE_B: RN14.5 (R4.2)

Notes on the sheet:
60.000MHz
Object Attribute Memory?
counters and shift registers.?
PRIORITY SPRITES
RAM DE VIDEO D0?
42.9545MHz
