jotego/jtcps/cores/cps3/sch/simm_main.kicad_sch

## KiCad design cores/cps3/sch/simm_main.kicad_sch (2022-11-22, an earlier design)

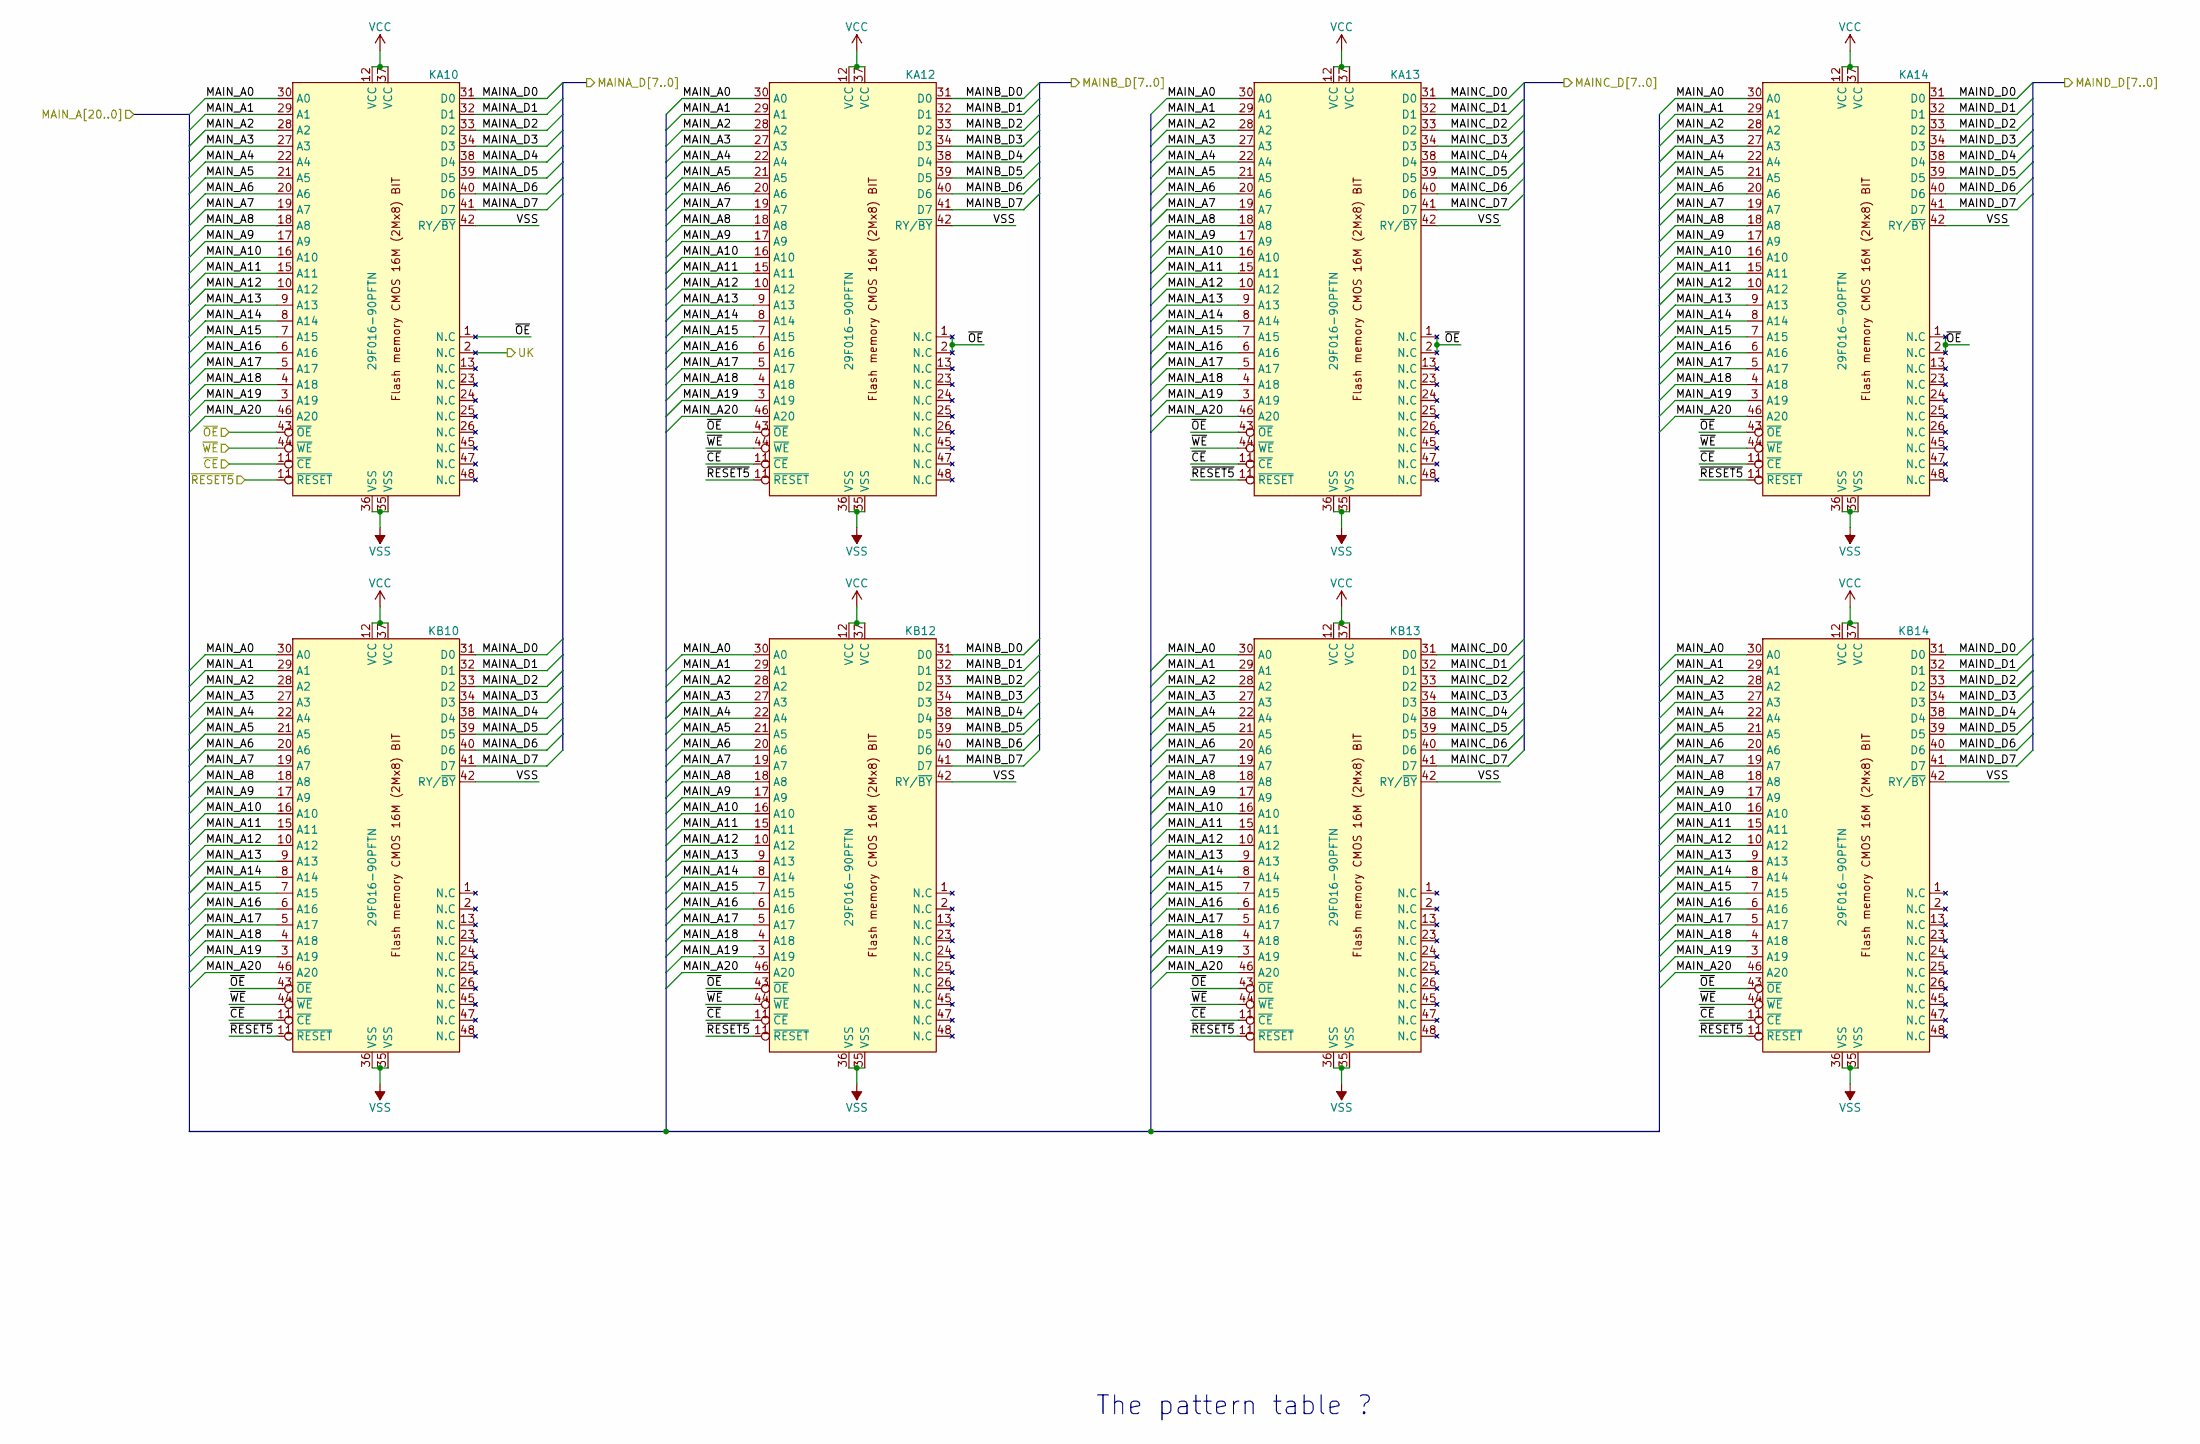
[picture p105: schematic simm_main.kicad_sch]

Parts:
KA10, KA12, KA13, KA14: 29F016-90PFTN
KB10, KB12, KB13, KB14: 29F016-90PFTN

Connections:
MAINA_D0: KA10.31 (D0), KB10.31 (D0)
MAINA_D1: KA10.32 (D1), KB10.32 (D1)
MAINA_D2: KA10.33 (D2), KB10.33 (D2)
MAINA_D3: KA10.34 (D3), KB10.34 (D3)
MAINA_D4: KA10.38 (D4), KB10.38 (D4)
MAINA_D5: KA10.39 (D5), KB10.39 (D5)
MAINA_D6: KA10.40 (D6), KB10.40 (D6)
MAINA_D7: KA10.41 (D7), KB10.41 (D7)
MAINB_D0: KA12.31 (D0), KB12.31 (D0)
MAINB_D1: KA12.32 (D1), KB12.32 (D1)
MAINB_D2: KA12.33 (D2), KB12.33 (D2)
MAINB_D3: KA12.34 (D3), KB12.34 (D3)
MAINB_D4: KA12.38 (D4), KB12.38 (D4)
MAINB_D5: KA12.39 (D5), KB12.39 (D5)
MAINB_D6: KA12.40 (D6), KB12.40 (D6)
MAINB_D7: KA12.41 (D7), KB12.41 (D7)
MAINC_D0: KA13.31 (D0), KB13.31 (D0)
MAINC_D1: KA13.32 (D1), KB13.32 (D1)
MAINC_D2: KA13.33 (D2), KB13.33 (D2)
MAINC_D3: KA13.34 (D3), KB13.34 (D3)
MAINC_D4: KA13.38 (D4), KB13.38 (D4)
MAINC_D5: KA13.39 (D5), KB13.39 (D5)
MAINC_D6: KA13.40 (D6), KB13.40 (D6)
MAINC_D7: KA13.41 (D7), KB13.41 (D7)
MAIND_D0: KA14.31 (D0), KB14.31 (D0)
MAIND_D1: KA14.32 (D1), KB14.32 (D1)
MAIND_D2: KA14.33 (D2), KB14.33 (D2)
MAIND_D3: KA14.34 (D3), KB14.34 (D3)
MAIND_D4: KA14.38 (D4), KB14.38 (D4)
MAIND_D5: KA14.39 (D5), KB14.39 (D5)
MAIND_D6: KA14.40 (D6), KB14.40 (D6)
MAIND_D7: KA14.41 (D7), KB14.41 (D7)
MAIN_A0: KA10.30 (A0), KA12.30 (A0), KA13.30 (A0), KA14.30 (A0), KB10.30 (A0), KB12.30 (A0), KB13.30 (A0), KB14.30 (A0)
MAIN_A1: KA10.29 (A1), KA12.29 (A1), KA13.29 (A1), KA14.29 (A1), KB10.29 (A1), KB12.29 (A1), KB13.29 (A1), KB14.29 (A1)
MAIN_A2: KA10.28 (A2), KA12.28 (A2), KA13.28 (A2), KA14.28 (A2), KB10.28 (A2), KB12.28 (A2), KB13.28 (A2), KB14.28 (A2)
MAIN_A3: KA10.27 (A3), KA12.27 (A3), KA13.27 (A3), KA14.27 (A3), KB10.27 (A3), KB12.27 (A3), KB13.27 (A3), KB14.27 (A3)
MAIN_A4: KA10.22 (A4), KA12.22 (A4), KA13.22 (A4), KA14.22 (A4), KB10.22 (A4), KB12.22 (A4), KB13.22 (A4), KB14.22 (A4)
MAIN_A5: KA10.21 (A5), KA12.21 (A5), KA13.21 (A5), KA14.21 (A5), KB10.21 (A5), KB12.21 (A5), KB13.21 (A5), KB14.21 (A5)
MAIN_A6: KA10.20 (A6), KA12.20 (A6), KA13.20 (A6), KA14.20 (A6), KB10.20 (A6), KB12.20 (A6), KB13.20 (A6), KB14.20 (A6)
MAIN_A7: KA10.19 (A7), KA12.19 (A7), KA13.19 (A7), KA14.19 (A7), KB10.19 (A7), KB12.19 (A7), KB13.19 (A7), KB14.19 (A7)
MAIN_A8: KA10.18 (A8), KA12.18 (A8), KA13.18 (A8), KA14.18 (A8), KB10.18 (A8), KB12.18 (A8), KB13.18 (A8), KB14.18 (A8)
MAIN_A9: KA10.17 (A9), KA12.17 (A9), KA13.17 (A9), KA14.17 (A9), KB10.17 (A9), KB12.17 (A9), KB13.17 (A9), KB14.17 (A9)
MAIN_A10: KA10.16 (A10), KA12.16 (A10), KA13.16 (A10), KA14.16 (A10), KB10.16 (A10), KB12.16 (A10), KB13.16 (A10), KB14.16 (A10)
MAIN_A11: KA10.15 (A11), KA12.15 (A11), KA13.15 (A11), KA14.15 (A11), KB10.15 (A11), KB12.15 (A11), KB13.15 (A11), KB14.15 (A11)
MAIN_A12: KA10.10 (A12), KA12.10 (A12), KA13.10 (A12), KA14.10 (A12), KB10.10 (A12), KB12.10 (A12), KB13.10 (A12), KB14.10 (A12)
MAIN_A13: KA10.9 (A13), KA12.9 (A13), KA13.9 (A13), KA14.9 (A13), KB10.9 (A13), KB12.9 (A13), KB13.9 (A13), KB14.9 (A13)
MAIN_A14: KA10.8 (A14), KA12.8 (A14), KA13.8 (A14), KA14.8 (A14), KB10.8 (A14), KB12.8 (A14), KB13.8 (A14), KB14.8 (A14)
MAIN_A15: KA10.7 (A15), KA12.7 (A15), KA13.7 (A15), KA14.7 (A15), KB10.7 (A15), KB12.7 (A15), KB13.7 (A15), KB14.7 (A15)
MAIN_A16: KA10.6 (A16), KA12.6 (A16), KA13.6 (A16), KA14.6 (A16), KB10.6 (A16), KB12.6 (A16), KB13.6 (A16), KB14.6 (A16)
MAIN_A17: KA10.5 (A17), KA12.5 (A17), KA13.5 (A17), KA14.5 (A17), KB10.5 (A17), KB12.5 (A17), KB13.5 (A17), KB14.5 (A17)
MAIN_A18: KA10.4 (A18), KA12.4 (A18), KA13.4 (A18), KA14.4 (A18), KB10.4 (A18), KB12.4 (A18), KB13.4 (A18), KB14.4 (A18)
MAIN_A19: KA10.3 (A19), KA12.3 (A19), KA13.3 (A19), KA14.3 (A19), KB10.3 (A19), KB12.3 (A19), KB13.3 (A19), KB14.3 (A19)
MAIN_A20: KA10.46 (A20), KA12.46 (A20), KA13.46 (A20), KA14.46 (A20), KB10.46 (A20), KB12.46 (A20), KB13.46 (A20), KB14.46 (A20)
unnamed: KA10.12 (VCC), KA10.37 (VCC)
unnamed: KA10.35 (VSS), KA10.36 (VSS)
unnamed: KA12.12 (VCC), KA12.37 (VCC)
unnamed: KA12.35 (VSS), KA12.36 (VSS)
unnamed: KA13.12 (VCC), KA13.37 (VCC)
unnamed: KA13.35 (VSS), KA13.36 (VSS)
unnamed: KA14.12 (VCC), KA14.37 (VCC)
unnamed: KA14.35 (VSS), KA14.36 (VSS)
unnamed: KB10.12 (VCC), KB10.37 (VCC)
unnamed: KB10.35 (VSS), KB10.36 (VSS)
unnamed: KB12.12 (VCC), KB12.37 (VCC)
unnamed: KB12.35 (VSS), KB12.36 (VSS)
unnamed: KB13.12 (VCC), KB13.37 (VCC)
unnamed: KB13.35 (VSS), KB13.36 (VSS)
unnamed: KB14.12 (VCC), KB14.37 (VCC)
unnamed: KB14.35 (VSS), KB14.36 (VSS)
UK: KA10.2 (N.C)
VSS: KA10.42 (RY/~BY), KA12.42 (RY/~BY), KA13.42 (RY/~BY), KA14.42 (RY/~BY), KB10.42 (RY/~BY), KB12.42 (RY/~BY), KB13.42 (RY/~BY), KB14.42 (RY/~BY)
~CE: KA10.11 (~CE), KA12.11 (~CE), KA13.11 (~CE), KA14.11 (~CE), KB10.11 (~CE), KB12.11 (~CE), KB13.11 (~CE), KB14.11 (~CE)
~OE: KA10.1 (N.C), KA10.43 (~OE), KA12.1 (N.C), KA12.2 (N.C), KA12.43 (~OE), KA13.1 (N.C), KA13.2 (N.C), KA13.43 (~OE), KA14.1 (N.C), KA14.2 (N.C), KA14.43 (~OE), KB10.43 (~OE), KB12.43 (~OE), KB13.43 (~OE), KB14.43 (~OE)
~RESET5: KA10.11 (~CE), KA12.11 (~CE), KA13.11 (~CE), KA14.11 (~CE), KB10.11 (~CE), KB12.11 (~CE), KB13.11 (~CE), KB14.11 (~CE)
~WE: KA10.44 (~WE), KA12.44 (~WE), KA13.44 (~WE), KA14.44 (~WE), KB10.44 (~WE), KB12.44 (~WE), KB13.44 (~WE), KB14.44 (~WE)

Notes on the sheet:
The pattern table ?
