jotego/jtcps/cores/cps2/hdl/jtcps2_fn_sbox.v

/*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
    Author: Jose Tejada Gomez. Twitter: @topapate
    Version: 1.0
    Date: 16-2-2021 */


module jtcps2_sbox_fn1_r1(
    input  [ 7:0] din,
    input  [23:0] key,
    output [ 7:0] dout
);

    jtcps2_sbox #(
        .LUT( {
        2'd3, 2'd1, 2'd0, 2'd2, 2'd3, 2'd1, 2'd3, 2'd2, 
        2'd2, 2'd2, 2'd3, 2'd2, 2'd1, 2'd2, 2'd2, 2'd1, 
        2'd0, 2'd0, 2'd1, 2'd0, 2'd0, 2'd3, 2'd1, 2'd1, 
        2'd1, 2'd3, 2'd1, 2'd3, 2'd0, 2'd0, 2'd2, 2'd2, 
        2'd2, 2'd1, 2'd1, 2'd1, 2'd2, 2'd3, 2'd3, 2'd2, 
        2'd2, 2'd2, 2'd3, 2'd1, 2'd2, 2'd1, 2'd1, 2'd1, 
        2'd2, 2'd1, 2'd3, 2'd0, 2'd3, 2'd0, 2'd2, 2'd3, 
        2'd1, 2'd1, 2'd0, 2'd1, 2'd0, 2'd2, 2'd2, 2'd0
        } ),
        .LOC( { 3'd0, 3'd0, 3'd6, 3'd5, 3'd4, 3'd3 } ),
        .OK ( 6'b00_1111 ))
    u_sbox_fn1_r1_0(
        .din ( din                  ),
        .key ( key[ 5:0 ]           ),
        .dout( { dout[6], dout[3] } )
    );

    jtcps2_sbox #(
        .LUT( {
        2'd0, 2'd0, 2'd3, 2'd2, 2'd3, 2'd1, 2'd3, 2'd2, 
        2'd2, 2'd2, 2'd3, 2'd1, 2'd1, 2'd3, 2'd2, 2'd3, 
        2'd1, 2'd2, 2'd1, 2'd0, 2'd2, 2'd1, 2'd1, 2'd1, 
        2'd1, 2'd3, 2'd3, 2'd3, 2'd2, 2'd3, 2'd1, 2'd0, 
        2'd3, 2'd3, 2'd3, 2'd0, 2'd3, 2'd2, 2'd2, 2'd1, 
        2'd2, 2'd0, 2'd0, 2'd0, 2'd3, 2'd1, 2'd3, 2'd2, 
        2'd3, 2'd2, 2'd0, 2'd0, 2'd0, 2'd1, 2'd2, 2'd1, 
        2'd1, 2'd1, 2'd1, 2'd2, 2'd2, 2'd2, 2'd0, 2'd3
        } ),
        .LOC( { 3'd0, 3'd7, 3'd4, 3'd2, 3'd1, 3'd0 } ),
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
        } ),
        .LOC( { 3'd7, 3'd6, 3'd5, 3'd4, 3'd3, 3'd2 } ),
        .OK ( 6'b11_1111 ))
    u_sbox_fn2_r4_3(
        .din ( din                  ),
        .key ( key[23:18]           ),
        .dout( { dout[6], dout[5] } )
    );

endmodule
