jotego/jtcps/cores/cps1/hdl/jtcps1_sound.v

/*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
    Author: Jose Tejada Gomez. Twitter: @topapate
    Version: 1.0
    Date: 28-1-2020 */

module jtcps1_sound(
    input                rst,
    input                clk,

    // Interface with main CPU
    input         [ 7:0] snd_latch0,
    input         [ 7:0] snd_latch1,
    input                enable_adpcm,
    input                enable_fm,
    input         [ 1:0] fxlevel,
    input                pcmfilter_en,

    // ROM
    output    reg [15:0] rom_addr,
    output    reg        rom_cs,
    input         [ 7:0] rom_data,
    input                rom_ok,

    // ADPCM ROM
    output        [17:0] adpcm_addr,
    output               adpcm_cs,
    input         [ 7:0] adpcm_data,
    input                adpcm_ok,

    // Sound output
    output signed [15:0] left,
    output signed [15:0] right,
    output               sample,
    output reg           peak
);

(*keep*) wire cen_fm, cen_fm2, cen_oki, nc, cpu_cen;
wire signed [13:0] oki_pre, oki_pole;
reg  signed [13:0] oki_mux;
wire        [ 6:0] pole_a;
wire signed [15:0] adpcm_snd;
wire signed [15:0] fm_left, fm_right;
wire               peak_l, peak_r;
wire               oki_sample;

localparam [7:0] FMGAIN = 8'h06;

wire [7:0] fmgain  = enable_fm    ? FMGAIN  : 8'h0;
reg  [7:0] pcmgain;

always @(posedge clk) begin
    peak <= peak_r | peak_l;
    if( enable_adpcm ) begin
        case( fxlevel )
            2'd0: pcmgain <= 8'h04;
            2'd1: pcmgain <= 8'h08;
            2'd2: pcmgain <= 8'h0C;
            2'd3: pcmgain <= 8'h10;
        endcase
    end else begin
        pcmgain <= 8'h0;
    end
    oki_mux <= pcmfilter_en ? oki_pole : oki_pre;
end

jtframe_mixer #(.W1(16),.WOUT(16)) u_left(
    .rst    ( rst       ),
    .clk    ( clk       ),
    .cen    ( 1'b1      ),
    // input signals
    .ch0    ( fm_left   ),
    .ch1    ( adpcm_snd ),
    .ch2    ( 16'd0     ),
    .ch3    ( 16'd0     ),
    // gain for each channel in 4.4 fixed point format
    .gain0  ( fmgain    ),
    .gain1  ( pcmgain   ),
    .gain2  ( 8'h00     ),
    .gain3  ( 8'h00     ),
    .mixed  ( left      ),
    .peak   ( peak_l    )
);

jtframe_mixer #(.W1(16),.WOUT(16)) u_right(
    .rst    ( rst       ),
    .clk    ( clk       ),
    .cen    ( 1'b1      ),
    // input signals
    .ch0    ( fm_right  ),
    .ch1    ( adpcm_snd ),
    .ch2    ( 16'd0     ),
    .ch3    ( 16'd0     ),
    // gain for each channel in 4.4 fixed point format
    .gain0  ( fmgain    ),
    .gain1  ( pcmgain   ),
    .gain2  ( 8'h00     ),
    .gain3  ( 8'h00     ),
    .mixed  ( right     ),
    .peak   ( peak_r    )
);

jtframe_cen3p57 u_fmcen(
    .clk        (  clk       ),       // 48 MHz
    .cen_3p57   (  cen_fm    ),
    .cen_1p78   (  cen_fm2   )
);

jtframe_frac_cen u_okicen(
    .clk        (  clk              ),
    .n          ( 10'd1             ),
    .m          ( 10'd48            ),
    .cen        ( { nc, cen_oki }   ),
    .cenb       (                   )
);

(*keep*) wire [15:0] A;
(*keep*) reg  fm_cs, latch0_cs, latch1_cs, ram_cs, oki_cs, oki7_cs, bank_cs;
(*keep*) reg  oki7;
(*keep*) wire mreq_n, int_n;
wire WRn, oki_wrn;

reg  bank;
wire  io_cs = !mreq_n && A[15:12] == 4'b1111;

wire [7:0] oki_dout;
wire rd_n;
wire wr_n;

assign oki_wrn = ~(oki_cs & ~WRn);

always @(posedge clk) begin
    if ( rst ) begin
        rom_cs    <= 1'b0;
        rom_addr  <= 16'd0;
        ram_cs    <= 1'b0;
        fm_cs     <= 1'b0;
        oki_cs    <= 1'b0;
        bank_cs   <= 1'b0;
        oki7_cs   <= 1'b0;
        latch0_cs <= 1'b0;
        latch1_cs <= 1'b0;
    end else begin
        rom_cs    <= !mreq_n && !rd_n && (!A[15] || A[15:14]==2'b10);
        rom_addr  <= A[15] ? { 1'b1, bank, A[13:0] } : { 1'b0, A[14:0] };
        ram_cs    <= !mreq_n && A[15:12] == 4'b1101;
        fm_cs     <= io_cs && A[3:1]==3'd0;
        oki_cs    <= io_cs && A[3:1]==3'd1;
        bank_cs   <= io_cs && A[3:1]==3'd2;
        oki7_cs   <= io_cs && A[3:1]==3'd3;
        latch0_cs <= io_cs && A[3:1]==3'd4;
        latch1_cs <= io_cs && A[3:1]==3'd5;
    end
end

wire RAM_we = ram_cs && !WRn;
wire [7:0] ram_dout, dout, fm_dout;

assign WRn = wr_n | mreq_n;

always @(posedge clk, posedge rst) begin
    if(rst) begin
        bank <= 1'b0;
        oki7 <= 1'b0;
    end else if(!wr_n && cen_fm) begin
        if(bank_cs) bank <= dout[0];
        if(oki7_cs) oki7 <= dout[0];
    end
end

jtframe_ram #(.aw(11)) u_ram(
    .clk    ( clk      ),
    .cen    ( 1'b1     ),
    .data   ( dout     ),
    .addr   ( A[10:0]  ),
    .we     ( RAM_we   ),
    .q      ( ram_dout )
);

// As we operate much faster than cen_fm, the input data mux is done
// in two clock cycles. Data will always be ready before next cen_fm pulse
//
reg [7:0] din, cmd_latch, dev_latch, mem_latch;
reg       latch_cs, dev_cs, mem_cs, rom_ok2;

always @(posedge clk, posedge rst) begin
    if( rst ) begin
        din     <= 8'hff;
        rom_ok2 <= 1'b0;
    end
    else begin
        cmd_latch <= latch0_cs ? snd_latch0 : snd_latch1;
        latch_cs  <= latch1_cs | latch0_cs;
        dev_latch <= fm_cs ? fm_dout : oki_dout;
        dev_cs    <= fm_cs | oki_cs;
        mem_latch <= ram_cs ? ram_dout : rom_data;
        mem_cs    <= ram_cs | rom_cs;
        rom_ok2   <= rom_ok;
        case( 1'b1 )
            dev_cs:    din <= dev_latch;
            latch_cs:  din <= cmd_latch;
            mem_cs:    din <= mem_latch;
            default:   din <= 8'hff;
        endcase
    end
end

wire iorq_n, m1_n;
// wire irq_ack = !iorq_n && !m1_n;

jtframe_z80_romwait u_cpu(
    .rst_n      ( ~rst        ),
    .clk        ( clk         ),
    .cen        ( cen_fm      ),
    .cpu_cen    ( cpu_cen     ),
    .int_n      ( int_n       ),
    .nmi_n      ( 1'b1        ),
    .busrq_n    ( 1'b1        ),
    .m1_n       ( m1_n        ),
    .mreq_n     ( mreq_n      ),
    .iorq_n     ( iorq_n      ),
    .rd_n       ( rd_n        ),
    .wr_n       ( wr_n        ),
    .rfsh_n     (             ),
    .halt_n     (             ),
    .busak_n    (             ),
    .A          ( A           ),
    .din        ( din         ),
    .dout       ( dout        ),
    // manage access to ROM data from SDRAM
    .rom_cs     ( rom_cs      ),
    .rom_ok     ( rom_ok & rom_ok2     )
);

jt51 u_jt51(
    .rst        ( rst       ), // reset
    .clk        ( clk       ), // main clock
    .cen        ( cen_fm    ),
    .cen_p1     ( cen_fm2   ),
    .cs_n       ( !fm_cs    ), // chip select
    .wr_n       ( WRn       ), // write
    .a0         ( A[0]      ),
    .din        ( dout      ), // data in
    .dout       ( fm_dout   ), // data out
    .ct1        (           ),
    .ct2        (           ),
    .irq_n      ( int_n     ),  // I do not synchronize this signal
    // Low resolution output (same as real chip)
    .sample     ( sample    ), // marks new output sample
    .left       (           ),
    .right      (           ),
    // Full resolution output
    .xleft      ( fm_left   ),
    .xright     ( fm_right  )
);

assign adpcm_cs = 1'b1;
assign pole_a = oki7 ? 7'd108 : 7'd104; // Pole at 770 Hz

jt6295 #(.INTERPOL(1)) u_adpcm(
    .rst        ( rst       ),
    .clk        ( clk       ),
    .cen        ( cen_oki   ),
    .ss         ( oki7      ),
    // CPU interface
    .wrn        ( oki_wrn   ),  // active low
    .din        ( dout      ),
    .dout       ( oki_dout  ),
    // ROM interface
    .rom_addr   ( adpcm_addr),
    .rom_data   ( adpcm_data),
    .rom_ok     ( adpcm_ok  ),
    // Sound output
    .sound      ( oki_pre   ),
    .sample     ( oki_sample)   // ~26kHz
);

jtframe_pole #(.WS(14)) u_pole(
    .rst        ( rst       ),
    .clk        ( clk       ),
    .sample     ( oki_sample),
    .a          ( pole_a    ),
    .sin        ( oki_pre   ),
    .sout       ( oki_pole  )
);

jtframe_uprate2_fir u_fir1(
    .rst        ( rst            ),
    .clk        ( clk            ),
    .sample     ( oki_sample     ),
    .upsample   (                ), // ~52kHz, close to JT51's 55kHz
    .l_in       ({oki_mux,2'd0}  ),
    .r_in       (     16'd0      ),
    .l_out      ( adpcm_snd      ),
    .r_out      (                )
);

endmodule
