jotego/jtcps/cores/cps2/hdl/jtcps2_raster.v

/*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
    Author: Jose Tejada Gomez. Twitter: @topapate
    Version: 1.0
    Date: 28-1-2021 */

// Two line counters plus one pixel counter

module jtcps2_raster(
    input              rst,
    input              clk,
    input              pxl_cen,

    input              frame_start,
    input              line_inc,

    // interface with CPU
    input       [ 2:0] cnt_sel,
    input              wrn,
    input       [15:0] cpu_dout,
    output reg  [ 8:0] cnt_dout,

    output reg         raster       // raster event
);

wire [8:0] dout0, dout1, dout2, din;
wire [2:0] we, zero;
wire       mode;
wire       step, restart;
reg        cnt4; // 4MHz
wire       cen4;
wire       set_irq = zero[2] & (|zero[1:0]);
reg        irqsh;

assign cen4  = pxl_cen & cnt4;
assign mode  = cpu_dout[15];    // 1 will update the count immediately,
                                // 0 updates it on the next frame
assign din   = cpu_dout[8:0];
assign we    = {3{~wrn}} & cnt_sel;

assign step    = pxl_cen && line_inc;
assign restart = pxl_cen && frame_start; // a line count of 0x106 won't
                // cause an interrupt. I think that is the correct behaviour

always @(posedge clk) begin
    cnt_dout <= cnt_sel[0] ? dout0 : (cnt_sel[1] ? dout1 : dout2);
    if( pxl_cen ) begin
        cnt4    <= ~cnt4;
    end
    // interrupt pulse lasts at least one pixel, so the CPU cupnowcan
    // catch it
    if( set_irq )
        { raster, irqsh } <= 2'b11;
    else if( pxl_cen ) begin
        { raster, irqsh } <= { irqsh, 1'b0 };
    end
end

initial begin
    cnt4 = 0;
end

jtcps2_raster_cnt u_cnt0(
    .rst    ( rst       ),
    .clk    ( clk       ),
    .cen4   ( cen4      ),

    .restart( restart   ),
    .step   ( step      ),

    .we     ( we[0]     ),
    .mode   ( mode      ),
    .din    ( din       ),
    .dout   ( dout0     ),

    .zero   ( zero[0]   )
);

jtcps2_raster_cnt u_cnt1(
    .rst    ( rst       ),
    .clk    ( clk       ),
    .cen4   ( cen4      ),

    .restart( restart   ),
    .step   ( step      ),

    .we     ( we[1]     ),
    .mode   ( mode      ),
    .din    ( din       ),
    .dout   ( dout1     ),

    .zero   ( zero[1]   )
);

// Pixel counter
jtcps2_raster_pxlcnt u_cnt2(
    .rst    ( rst       ),
    .clk    ( clk       ),
    .pxl_cen( pxl_cen   ),
    .cen4   ( cen4      ),

    .restart( step      ), // Line start

    .we     ( we[2]     ),
    .din    ( din       ),
    .dout   ( dout2     ),

    .zero   ( zero[2]   )
);
endmodule

module jtcps2_raster_cnt(
    input              rst,
    input              clk,
    input              cen4,

    input              restart,
    input              step,

    input              we,
    input              mode,
    input       [ 8:0] din,
    output reg  [ 8:0] dout,

    output reg         zero       // raster event
);

reg  [8:0] cnt_start, cnt;
reg        upnow;

always @(posedge clk, posedge rst) begin
    if( rst ) begin
        cnt       <= ~9'd0;
        cnt_start <= ~9'd0;
        dout      <= ~9'd0;
        upnow     <= 0;
        zero      <= 0;
    end else begin
        zero <= ~|cnt;
        if(cen4) dout <= cnt;
        if( we ) begin
            cnt_start <= din;
            upnow     <= mode ;
        end
        if( upnow&&we )
            cnt <= din;
        else if( step )
            cnt <= restart ? cnt_start : cnt-9'd1;
    end
end

endmodule

module jtcps2_raster_pxlcnt(
    input              rst,
    input              clk,
    input              pxl_cen,
    input              cen4,

    input              restart,

    input              we,
    input       [ 8:0] din,
    output      [ 8:0] dout,

    output reg         zero       // raster event
);

reg  [8:0] cnt_start;
reg  [7:0] cnt, preout;
reg        pulse4;
//wire       cen4b;

//assign cen4b = pxl_cen & ~cen4;
assign dout  = { preout, cnt_start[0] ^ ~pulse4 };

always @(posedge clk, posedge rst) begin
    if( rst ) begin
        cnt       <= ~8'd0;
        cnt_start <= ~9'd0;
        preout    <= ~8'd0;
        pulse4    <= 0;
    end else begin
        if( pxl_cen ) pulse4 <= cen4; // pulse4 must be deterministic
                                      // and independent of reset for dout[0]
                                      // to work as expected
        if( cen4 ) preout <= cnt;
        if( pxl_cen ) begin
            if( cen4^~cnt_start[0]) // This is an odd way of counting 9 bits
                zero <= ~|cnt;      // but it follows the original design
            else
                zero <= 0;
        end

        if( we ) begin
            cnt_start <= din;
        end
        if( restart )
            cnt <= cnt_start[8:1];
        else if( cen4 )
            cnt <= cnt-8'd1;
    end
end

endmodule
